EleonoreMizo/pedalevite/src/mfx/dsp/nz/README.md

## nz — noise generators

- **`GaussFast`**: fast gaussian noise approximation
- **`PinkShade`**: accurate pink noise generator
- **`WhiteFast`**: rough but very fast white noise generator
