EleonoreMizo/pedalevite/doc/v1/datasheets/DFRobot 128x64 display/12864B_Graphic_LCD_Module_Dimensions.jpg

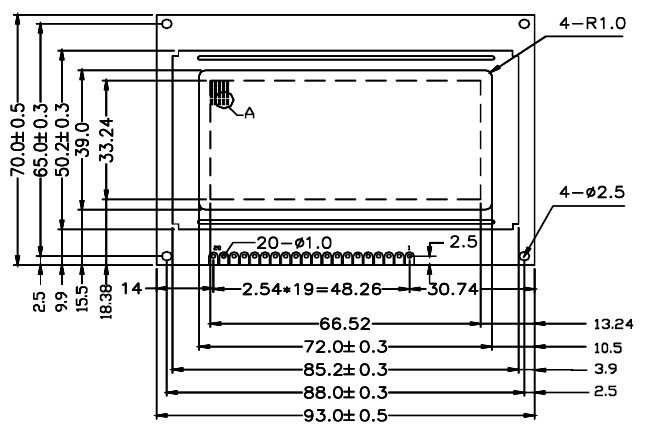
doc/v1/datasheets/DFRobot 128x64 display/12864B_Graphic_LCD_Module_Dimensions.jpg
