EleonoreMizo/pedalevite/doc/v1/datasheets/Toowei T601/ABUIABACGAAg-rylwQUoh9G9lAcwxgU46QE.jpg

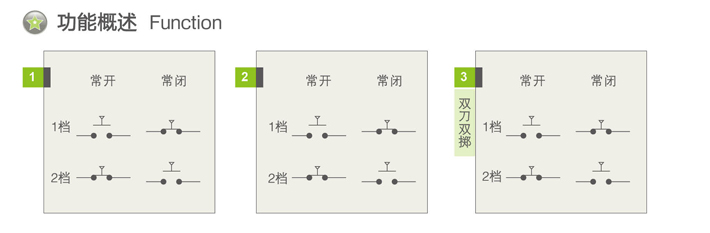
doc/v1/datasheets/Toowei T601/ABUIABACGAAg-rylwQUoh9G9lAcwxgU46QE.jpg
