EleonoreMizo/pedalevite/doc/v1/datasheets/Toowei T601/ABUIABACGAAg_rylwQUorPvk0wEwxgU44gU.jpg

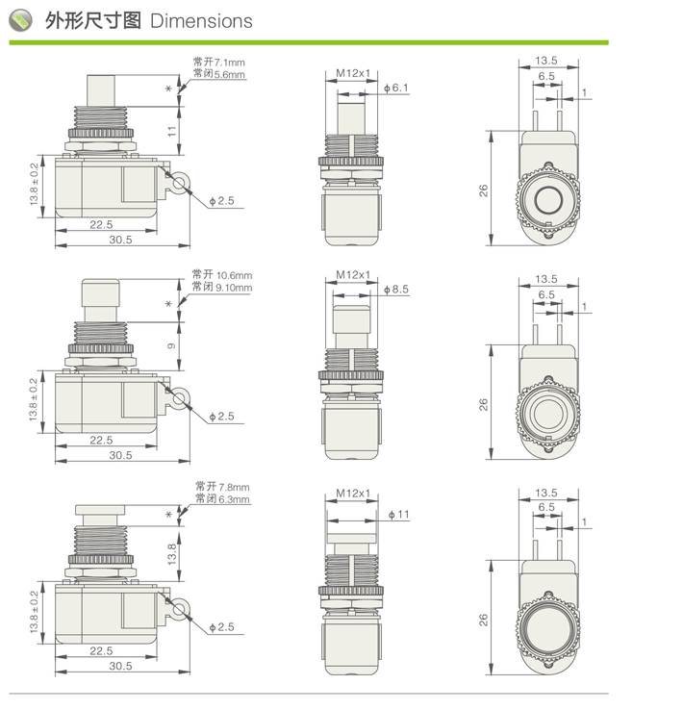
doc/v1/datasheets/Toowei T601/ABUIABACGAAg_rylwQUorPvk0wEwxgU44gU.jpg
