EleonoreMizo/pedalevite/doc/v1/datasheets/Toowei T601/ABUIABACGAAggbfIvgUoiN_t6AIw6AI4-AE.jpg

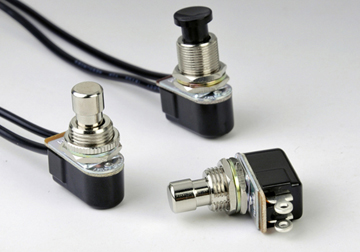
doc/v1/datasheets/Toowei T601/ABUIABACGAAggbfIvgUoiN_t6AIw6AI4-AE.jpg
