EleonoreMizo/pedalevite/doc/v1/datasheets/Toowei T601/ABUIABACGAAggL2lwQUo4-u1sgYwxgU4ywE.jpg

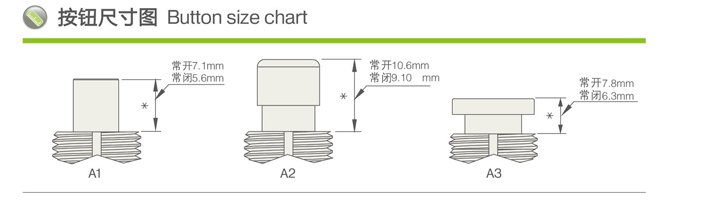
doc/v1/datasheets/Toowei T601/ABUIABACGAAggL2lwQUo4-u1sgYwxgU4ywE.jpg
