EleonoreMizo/pedalevite/doc/v1/datasheets/Toowei T601/ABUIABACGAAggr2lwQUolMDTvAcwxgU40AE.jpg

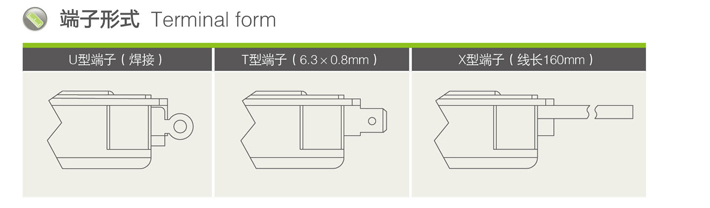
doc/v1/datasheets/Toowei T601/ABUIABACGAAggr2lwQUolMDTvAcwxgU40AE.jpg
