EleonoreMizo/pedalevite/doc/v1/datasheets/Toowei T601/ABUIABACGAAgt6LAwAUotr7NzQMwxgU4vwI.jpg

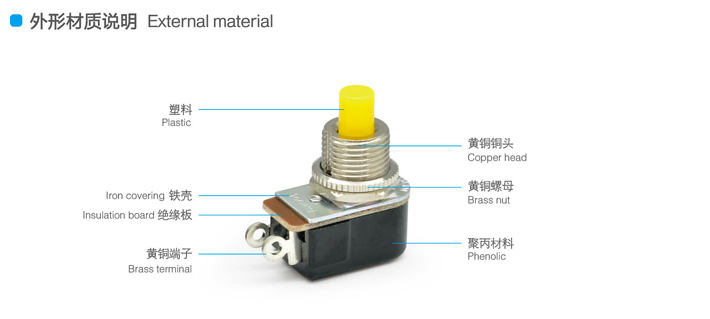
doc/v1/datasheets/Toowei T601/ABUIABACGAAgt6LAwAUotr7NzQMwxgU4vwI.jpg
