EleonoreMizo/pedalevite/doc/v1/datasheets/Toowei T601/ABUIABACGAAgtaLAwAUo_Jv2oAEwxgU4yAE.jpg

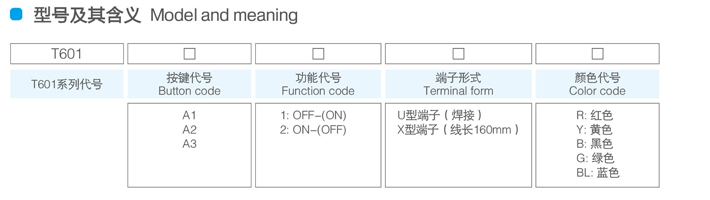
doc/v1/datasheets/Toowei T601/ABUIABACGAAgtaLAwAUo_Jv2oAEwxgU4yAE.jpg
