EleonoreMizo/pedalevite/doc/v1/datasheets/Toowei T601/ABUIABACGAAgtY63wAUo7P-HVTDGBTjEBw.jpg

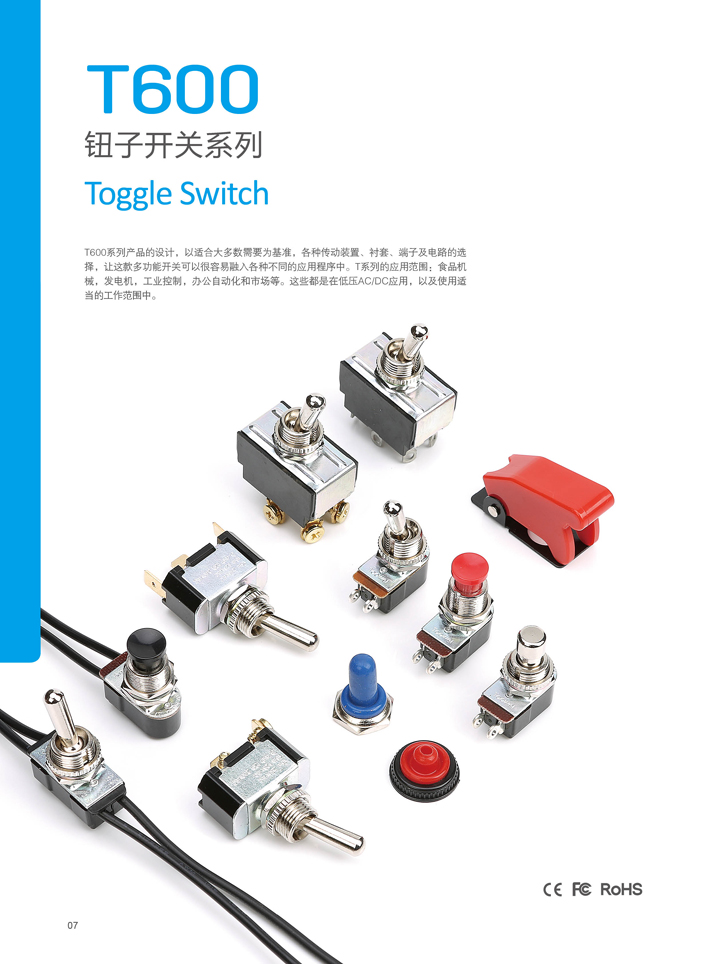
doc/v1/datasheets/Toowei T601/ABUIABACGAAgtY63wAUo7P-HVTDGBTjEBw.jpg
