EleonoreMizo/pedalevite/doc/v1/datasheets/Toowei T601/ABUIABACGAAguaLAwAUoiPfkyAMwxgU4rgI.jpg

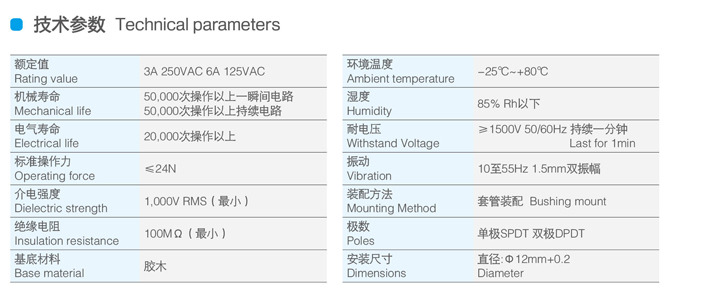
doc/v1/datasheets/Toowei T601/ABUIABACGAAguaLAwAUoiPfkyAMwxgU4rgI.jpg
