EleonoreMizo/pedalevite/doc/v1/building-instructions/index-eng.html

# Pédale Vite — Building instructions

## Table of content

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

## I. Introduction

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

## II. Required materials

The project’s GitHub repository (https://github.com/EleonoreMizo/pedalevite/) contains all the required files.

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

Some documents have been exported to .png or .pdf for convenience.

### Drawings

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

### Materials

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

### Tools

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

## III. Step-by-step building

### Enclosure

#### Machining

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

Pictures with some elements mounted:





#### Folding

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

The plate (without anything mounted) will be sandwiched between two devices.

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

#### Side stands

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

#### Stand for the Pi

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

### Electronics

#### Prototyping board cutting

Cut the prototyping boards in order to obtain the following pieces:

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



#### Soldering

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

#### Connection checks

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

#### LED board

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

#### Rotary encoder board

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

#### Display fix board

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

#### Wiring

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

### Assembly

#### First assembly

Most parts can now be screwed to the enclosure: boards, plugs, switches…



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

#### Soldering the switches

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

Also, depending on the model you got, the plastic box may be quite sensitive to heat and could melt easily. If one of the pin just slightly moves during soldering, the contact may be damaged. If it happens on DPDT switches, you can desolder it and try the other path. Always check the contact with a multimeter once both pins are soldered.

When all footswitch wires are soldered, they can be grouped by connector.



#### Soldering the power cables

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

Finally, connect the switch to the C14 socket using the remaining pins.

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



#### Soldering the audio cables

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

Solder a male jack plug to each of these cables.

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

Finally, solder the cables for the expression pedals.



#### Internal USB cable

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

Finally, solder the cable screen to the plug.

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



#### Power supply for the audio interface

Build a cable with three parts the following way:

First part is the power supply whose plug has been cut. Strip the wires.

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

Possibly: add an RC filter (not described here) if the power supply is too cheap.

#### Base of the enclosure

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

Calibrate the audio interface (gain and volume knobs) before closing the box.

For the enclosure feets, you can use specific rubber parts fitting on the screws.

## IV. Software setup

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

### Preparing the system

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

Unpack somewhere the .img file contained in the archive.

First format the card, if not previously done:

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

### Startup and base configuration

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

Log in with the default identifiers (pi / raspberry).

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

sudo nano /boot/config.txt

Modify the following lines by commenting or uncommenting them, as follows:

dtparam=i2c_arm=on
dtparam=spi=on
#dtparam=audio=on

Therefore the default audio device is removed. This is important because it simplifies our audio interface installation. Then, we ask to load the I2C module during boot:

sudo nano /etc/modules

Add the following lines at the end of the file:

i2c-bcm2708
i2c-dev

We now ask to boot to the command line to avoid loading the graphical interface subsystem:

sudo systemctl set-default multi-user.target
sudo ln -fs /lib/systemd/system/getty@.service \
/etc/systemd/system/getty.target.wants/getty@tty1.service

Now you can set your language and keyboard preferences (optional):

sudo raspi-config

Select 4. Localisation Options and set your language and keyboard preferences. Finally, hit the left arrow to select Finish. Reboot if the program requires it:

sudo shutdown -r now

### System update

Update the system:

sudo apt-get -y update
sudo apt-get -y dist-upgrade

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

### Installing the audio interface

Plug the interface. Open a console and type:

aplay -l

The USB interface should be on the list. Then, edit:

sudo nano /lib/modprobe.d/aliases.conf

Comment the line lowering the priority of USB interfaces:

#options snd-usb-audio index=-2

Reboot to validate the parameters.

sudo shutdown -r now

Log in again and type:

cat /proc/asound/modules

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

aplay -v -D plughw:0,0 file.wav

The sound should play fine, without any glitch.

### Software dependencies

Install git, Jack2, ALSA and autoconf :

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

wiringPi has its own installing procedure:

git clone git://git.drogon.net/wiringPi
cd wiringPi
./build

### Installing Pédale Vite

First, download the code in ~/Documents.

cd ~
mkdir Documents
cd Documents
git clone https://github.com/EleonoreMizo/pedalevite.git

Compile:

cd pedalevite/build/unix
./autogen.sh
./configure-release
make -j4

Note : the configure script was renamed configure-v1-release in later releases.

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

sudo /opt/pedalevite/bin/pedalevite

The program should run normally. Ctrl+C to stop it.

### Pédale Vite autostart

Create this file:

sudo nano /etc/init.d/pedalevite

Modify the file the following way:

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

case "$1" in
    start)
        echo "Mounting Pedale Vite directory as R/W..."
	mount --bind /opt/pedalevite/ /opt/pedalevite/
	mount -o remount,rw /opt/pedalevite/
	echo "Starting Pedale Vite..."
	/opt/pedalevite/bin/pedalevite &
	echo -n performance | sudo tee /sys/devices/system/cpu/cpu0/cpufreq/scaling_governor
	;;
    stop)
	echo "Stopping Pedale Vite"
	killall pedalevite
        umount /opt/pedalevite/
	;;
    *)
	echo "Usage: /etc/init.d/pedalevite start|stop"
	exit 1
	;;
esac

exit 0

Then:

sudo chmod +x /etc/init.d/pedalevite
sudo update-rc.d pedalevite defaults

Pédale Vite will run automatically at the next reboot. It can be run immediately, too:

sudo /etc/init.d/pedalevite start

### Boot time optimisation

Edit the file:

sudo nano /etc/modprobe.d/raspi-blacklist.conf

Add the following lines to deactivate WiFi and Bluetooth :

#wifi
blacklist brcmfmac
blacklist brcmutil
#bluetooth
blacklist btbcm
blacklist hci_uart

### NOOBS removal

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

sudo fdisk -l

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

Mount the NOOBS partition:

sudo mkdir /mnt/noobs
sudo mount /dev/mmcblk0p1 /mnt/noobs

Create or modify autoboot.txt :

nano /mnt/noobs/autoboot.txt

Add the following line, possibly replacing the 6 with the desired partition number:

boot_partition=6

Reboot to check that everything is fine.

### Read-only operating system and other optimisations

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

sudo apt-get -y remove --purge wolfram-engine triggerhappy pi-bluetooth
sudo apt-get -y remove --purge cron anacron logrotate dphys-swapfile

Remove the X-server and related:

sudo apt-get -y remove --purge xserver-common lightdm
sudo insserv -r x11-common

Remove the now useless dependencies:

sudo apt-get -y autoremove --purge

Install busybox syslog instead of rsyslog :

sudo apt-get -y install busybox-syslogd
sudo dpkg --purge rsyslog

Change the location of the DHCP leases:

sudo rm -rf /var/lib/dhcp/
sudo rm -rf /var/lib/dhcpcd5/
sudo ln -s /tmp /var/lib/dhcp
sudo ln -s /tmp /var/lib/dhcpcd5
sudo rm /etc/resolv.conf
sudo ln -s /tmp/dhcpcd.resolv.conf /etc/resolv.conf

Replace some var subfolders with symbolic links on the RAM-disk:

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

Create or edit the /tmp/random-seed file at reboot:

sudo nano /lib/systemd/system/systemd-random-seed.service

Add a ExecStartPre line in [Services] :

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

Other details:

sudo nano /etc/init.d/checkroot.sh

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

case "$1" in
  start|"")
        #do_start
        ;;
  restart|reload|force-reload)

sudo nano /etc/init.d/checkfs.sh

Same, comment the do_start at the end if the file exists.

sudo nano /etc/init.d/checkroot-bootclean.sh

Comment the rm and the clean_all in the case start if the file exists

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

It’s not important if several of the commands above fail (“no such file or directory”).

sudo nano /etc/systemd/system/dhcpcd5.service

The file may also be called dhcpcd5. Modify it to put the PIDFile in /var :

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

sudo nano /etc/fstab

Add ,ro after the defaults for the disk patitions:

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

sudo nano /boot/cmdline.txt

Add fastboot noswap ro at the very end of the line:

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

mmcblk0p1 can change as well, depending on NOOBS.

sudo nano /etc/rc.local

Add the chmod before the exit 0:

  printf "My IP address is %s\n" "$_IP"
fi

chmod g+w,o+w /tmp
exit 0

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

sudo nano /etc/bash.bash_logout

Add the following lines at the end:

mount -o remount,ro /
mount -o remount,ro /boot

Notifies the changes to systemd:

sudo systemctl daemon-reload

Reboot. Pédale Vite is now functional.

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

Failed to get D-Bus connection: No such file or directory

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

sudo mount -o remount,rw /

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

sudo mount -o remount,rw /boot

## V. Maintenance

### Tests and troubleshooting

To do…

### Source code

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

#### Compiling

Project files are located in the pedalevite/build folder.

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

win contains the projects for Visual Studio 2013. Source code is organized according to seveal categories:

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

These three projects are bundled into the pedalevite.sln solution.

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

#elif (MAIN_API == MAIN_API_ASIO)
	mfx::adrv::DAsio  snd_drv;
	chn_idx_in = 2;
#else

The emulation uses the following keys:

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

#### Architecture

##### Threads

The program uses 3 main threads:

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

##### MVC paradigm

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

#### File tree

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

## VI. Possible improvements and variations

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

#### External audio interface

There would be some advantages to put the audio interface out of the perdalboard:

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

For the cons:

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

#### Cheaper parts

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

#### Rotary encoder removal

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

Less connections, less costs and a full board less. This is about 25€ saved.

#### Single PCB

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

Schematics remain the same, socket connectors too, excepted two of them.

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

#### Pull-up resistors

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

#### Soldering bridges for the display

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

#### Reducing the number of connectors

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

## VII. Version history

r3, 2020-01-16

- Added the creation of a few subdirectories for software installation.

r2, 2019-11-07

- Updated the autostart script to set the /opt/pedalevite subdirectory in R/W mode.

r1, 2017-09-24

- Document translation in English.

r0, 2016-12-31

- Document creation (in French).
