EleonoreMizo/pedalevite/doc/user-manual/sources/note.txt

screenshots.xcf :

– Crop
– Export to OpenRaster (.ora) format
– Rename the .ora to .zip
– Extract
– Use a spreasheet to turn the .xml index into a rename batch
