EleonoreMizo/pedalevite/doc/v1/user-manual/index.html

# Pédale Vite — manuel d’utilisation

## Table des matières

1. Introduction
2. Utilisation
  1. Description du matériel
  2. Démarrage
  3. Calibration
  4. Premiers pas
3. Référence
  1. Concepts
  2. Diodes lumineuses
  3. Écrans principaux
  4. Édition d’un programme
  5. Banques de programmes
  6. Configuration du pédalier
  7. Volumes et niveaux
  8. Réglages divers
  9. Accordeur
  10. Redémarrage
4. Effets disponibles
  1. All-Pass Distortion — Distorsion
  2. Color Me — Filtre de coloration vocale
  3. CompEx — Compresseur/Expanseur
  4. Convert To Stereo
  5. Delay — Écho stéréo
  6. Distortion Tone Stage — Tonalité pour distorsion
  7. Double Distortion
  8. Envelope Follower — Suiveur d’enveloppe
  9. Filter Squeezer — Filtre résonnant à distorsion
  10. FlanCho — Chorus et flanger
  11. Freeverb — Réverbération
  12. Frequency Shifter — Translateur de fréquences
  13. Harmonic Tremolo — Trémolo bi-bande
  14. Hypercomb — Filtre en peigne polyphonique
  15. Input Impedance Fix — Adaptation d’impédance d’entrée
  16. Noise Bleach — Barrière anti-bruit
  17. Noise Chlorine — Barrière anti-bruit
  18. Onset detector – Détecteur de début et de fin de note
  19. Parametric Equalizer — Égaliseur paramétrique
  20. Phaser AP
  21. Phaser HT
  22. Pitch Detector — Détecteur de hauteur de note
  23. Pulse Width Modulation Distortion
  24. Pulse Width Modulation Distortion 2
  25. SiemensGirlz — Écho créatif
  26. Simple Distortion
  27. Speaker Emulator — Émulation de haut-parleur
  28. Test Generator — Générateur de tonalités de test
  29. Tremolo
  30. Wah-wah
  31. Wah-wah (CryBaby)
  32. ADSR — Enveloppe de contrôle
  33. Control ramp — Transition de paramètre
  34. LFO — Oscillateur basse fréquence
5. Dépannage
6. Historique des versions

## I. Introduction

Pédale Vite est une pédalier multi-effet pour guitare à fabriquer soi-même (DIY, do it yourself). Ce manuel détaille comment utiliser le pédalier une fois monté et fonctionnel.

## II. Utilisation

### Description du matériel

#### Face arrière

1. Ports USB et Ethernet du Rasberry Pi 3
2. Prises pour pédales d’expression
3. Interrupteur de mise en marche
4. Cordon d’alimentation secteur 220–240 V
5. Sorties audio vers ampli ou console
6. Sortie casque, stéréo en jack 6,35 mm.
7. Entrées guitare



L’accès au Pi n’est pas nécessaire en fonctionnement courant et ne sert qu’aux opérations de maintenance.

La première pédale d’expression se trouve à gauche sur le panneau, et donc à droite quand on fait face au pédalier.

Tous les jacks sont en 6,35 mm et sont asymétriques (signal mono), à part la prise casque qui est stéréo.

Les canaux gauches et droits des entrées et des sorties sont inversés afin qu’ils soient dans le bon ordre quand on se place devant le pédalier. Les entrées font environ 500 kΩ d’impédance. Utiliser le canal gauche pour brancher la guitare ou tout autre signal mono. Quand le pédalier est configuré en mono, les deux sorties diffusent le même signal.

#### Face supérieure

8. Bouton de contrôle des effets
9. Écran
10. Boutons rotatifs de navigation dans les menus
11. Boutons de navigation dans les menus
12. LED de contrôle, leur usage dépend du contexte.
13. Deux rangées de six pédales permettant de changer les effets.



Les boutons poussoir de navigation sont agencés de la façon suivante. Sur la rangée supérieure : Sélectionner/valider (Select), flèche haut (↑), annuler/échappement (Esc). Sur la rangée inférieure : flèches gauche (←), bas (↓), droite (→).

Les boutons rotatifs de navigation sont généralement redondants des boutons poussoir. Celui de gauche permet de se déplacer verticalement, et celui de droite horizontalement.

### Démarrage



1. Brancher le cordon d’alimentation (4) sur le secteur.
2. Brancher la guitare à l’entrée gauche (7).
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
