EleonoreMizo/pedalevite/doc/building-instructions/board-5v-wires.jpg

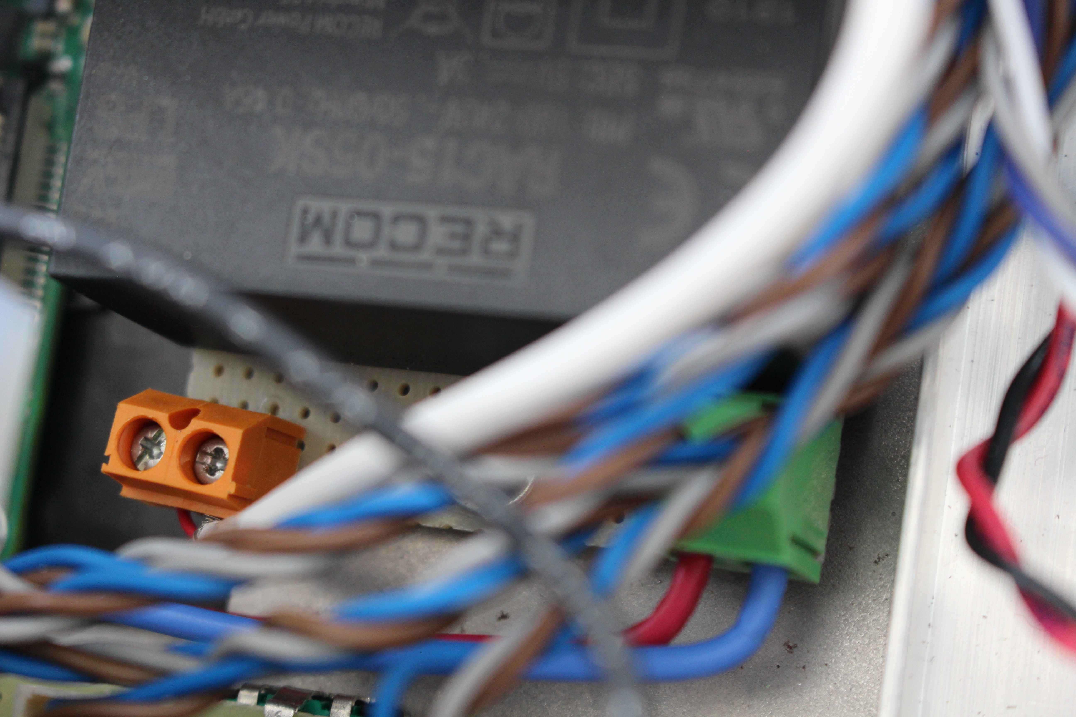
doc/building-instructions/board-5v-wires.jpg
