EleonoreMizo/pedalevite/doc/building-instructions/board-audio-input.jpg

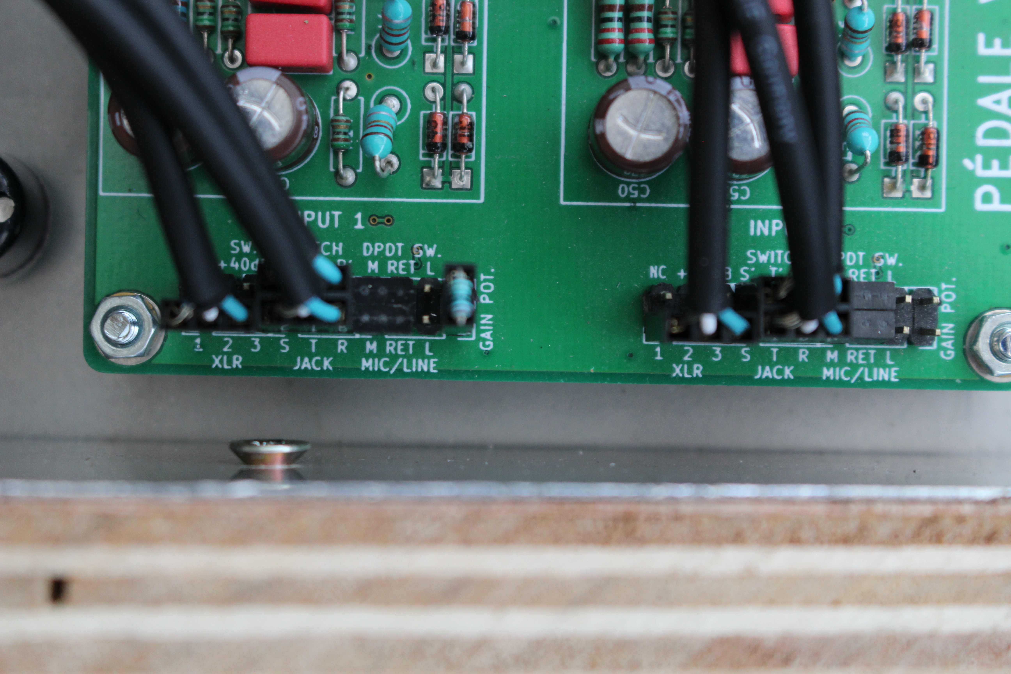
doc/building-instructions/board-audio-input.jpg
