EleonoreMizo/pedalevite/doc/building-instructions/board-audio-jumper-gnd.jpg

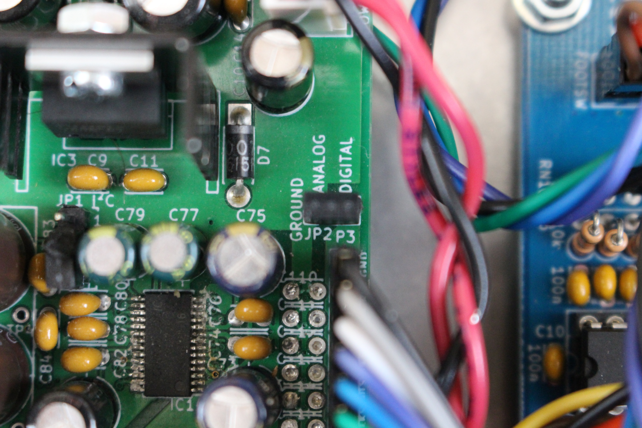
doc/building-instructions/board-audio-jumper-gnd.jpg
