EleonoreMizo/pedalevite/doc/building-instructions/board-audio-jumper-i2c.jpg

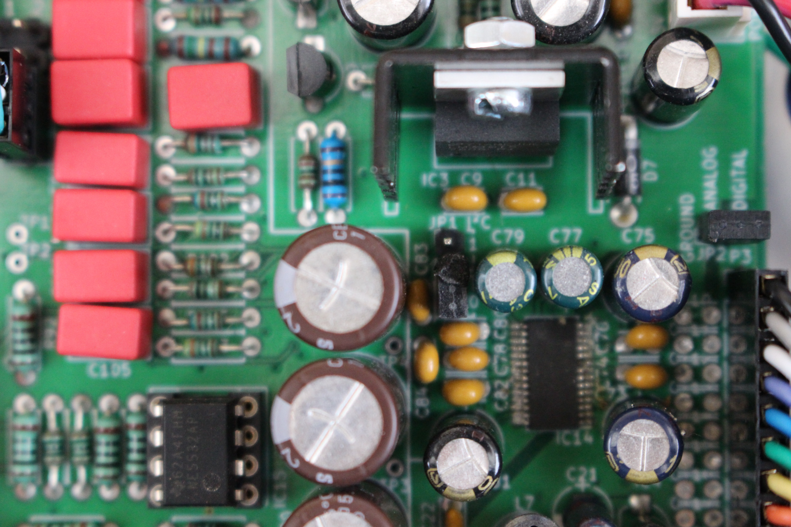
doc/building-instructions/board-audio-jumper-i2c.jpg
