EleonoreMizo/pedalevite/doc/building-instructions/board-audio-output.jpg

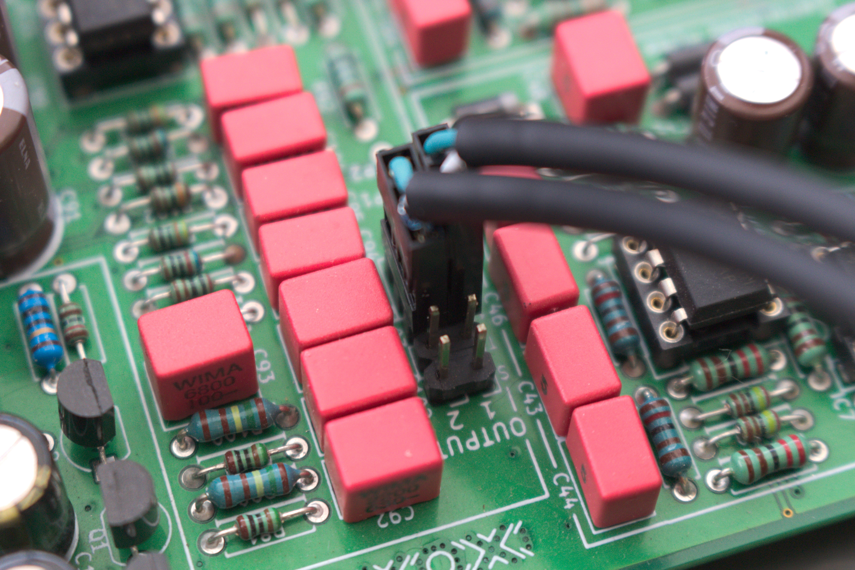
doc/building-instructions/board-audio-output.jpg
