EleonoreMizo/pedalevite/doc/building-instructions/board-audio.jpg

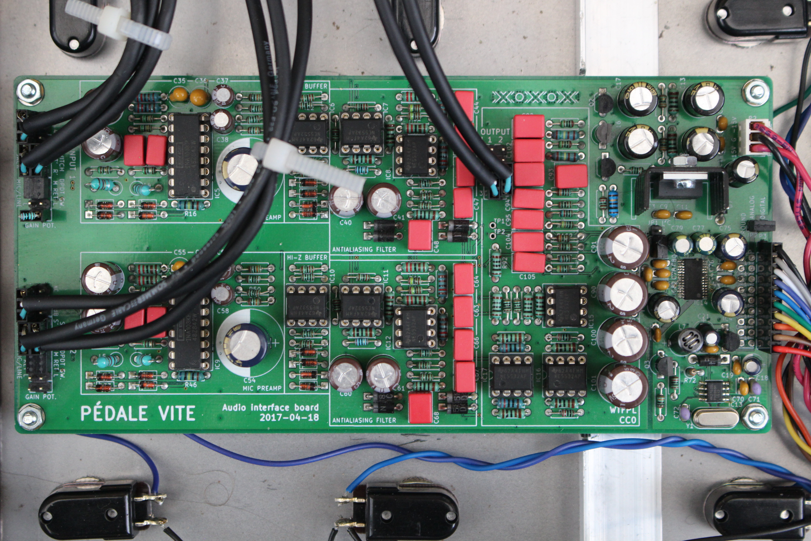
doc/building-instructions/board-audio.jpg
