EleonoreMizo/pedalevite/doc/building-instructions/board-rot-enc-nav.jpg

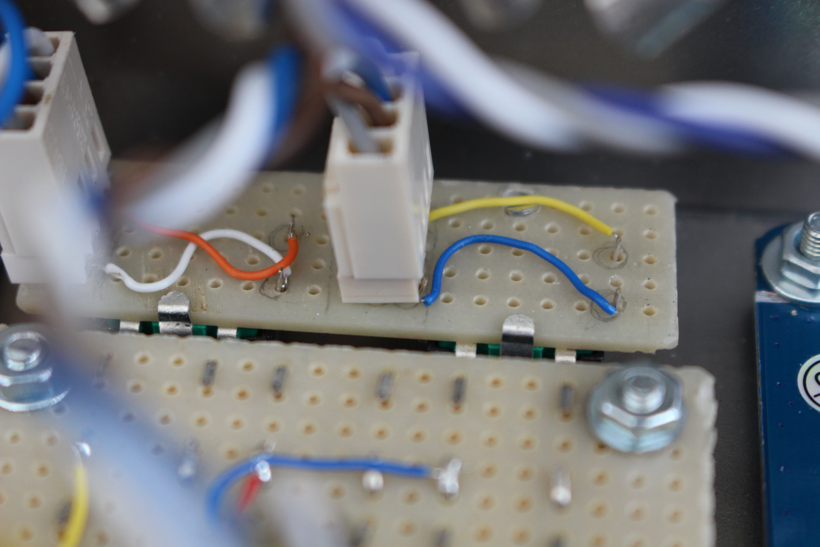
doc/building-instructions/board-rot-enc-nav.jpg
