EleonoreMizo/pedalevite/doc/building-instructions/board-rot-enc-param.jpg

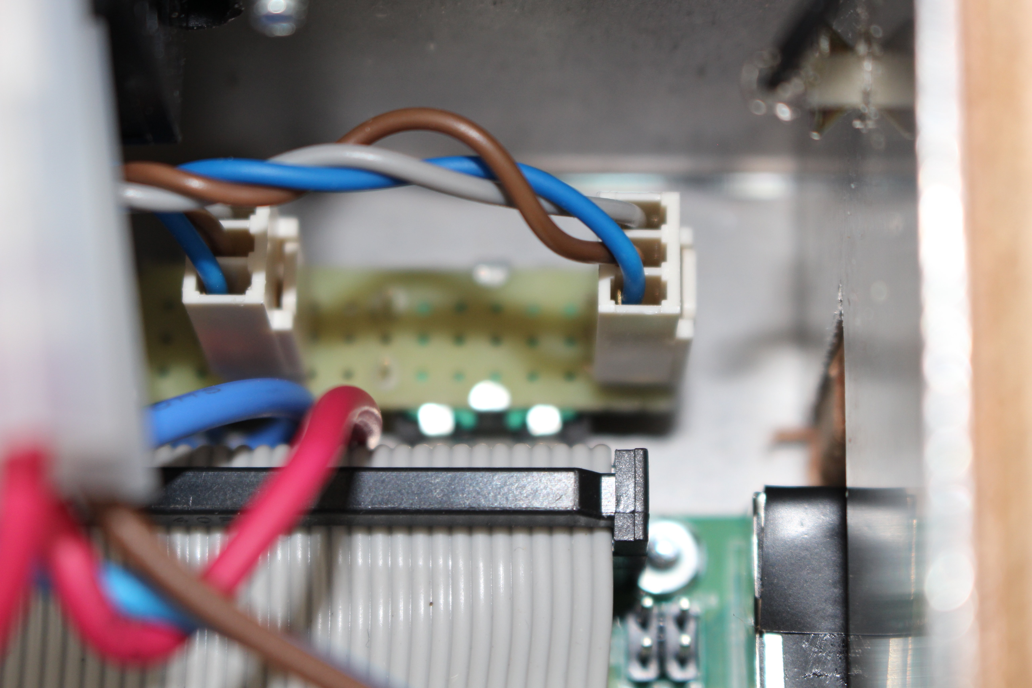
doc/building-instructions/board-rot-enc-param.jpg
