EleonoreMizo/pedalevite/doc/building-instructions/cables-mains.jpg

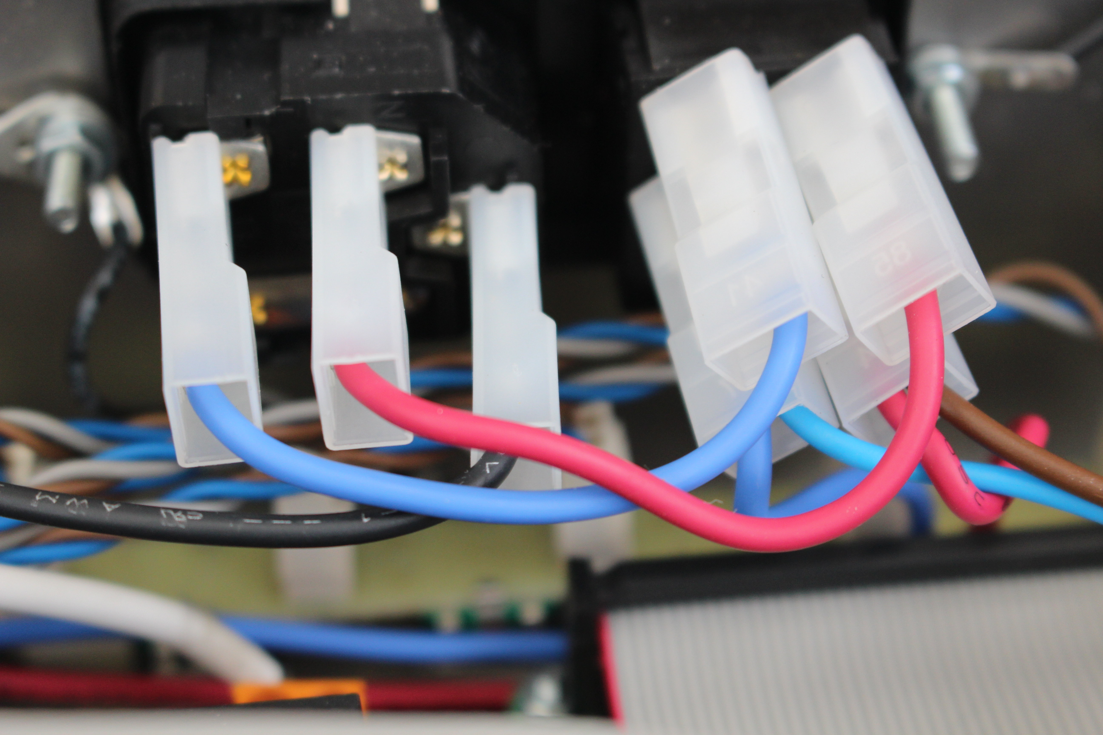
doc/building-instructions/cables-mains.jpg
