EleonoreMizo/pedalevite/doc/building-instructions/connectors-expression-pedals.jpg

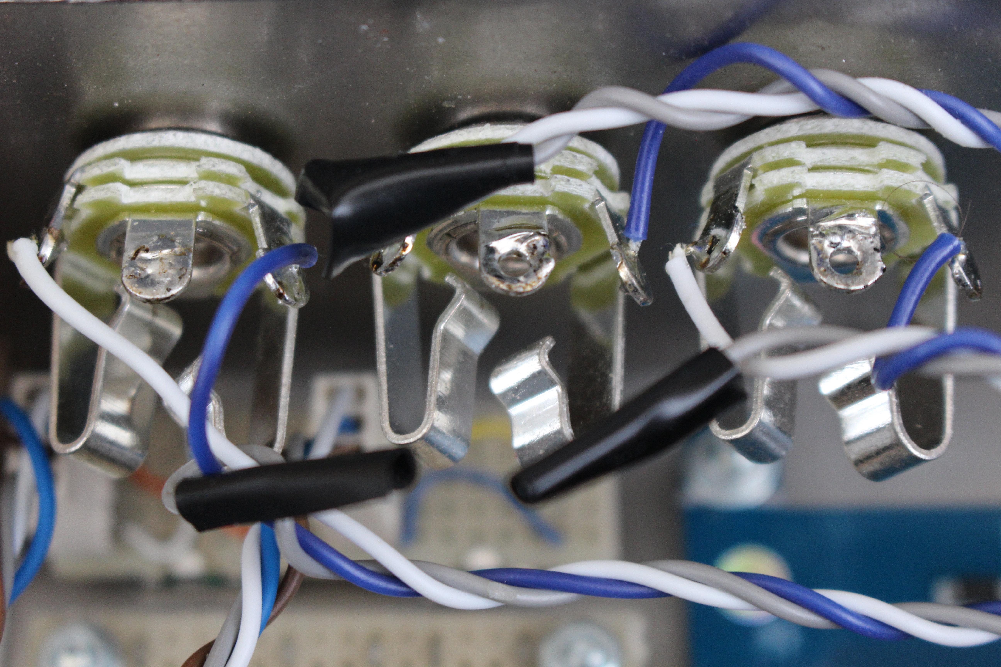
doc/building-instructions/connectors-expression-pedals.jpg
