EleonoreMizo/pedalevite/doc/building-instructions/connectors-missing-gain-pad.jpg

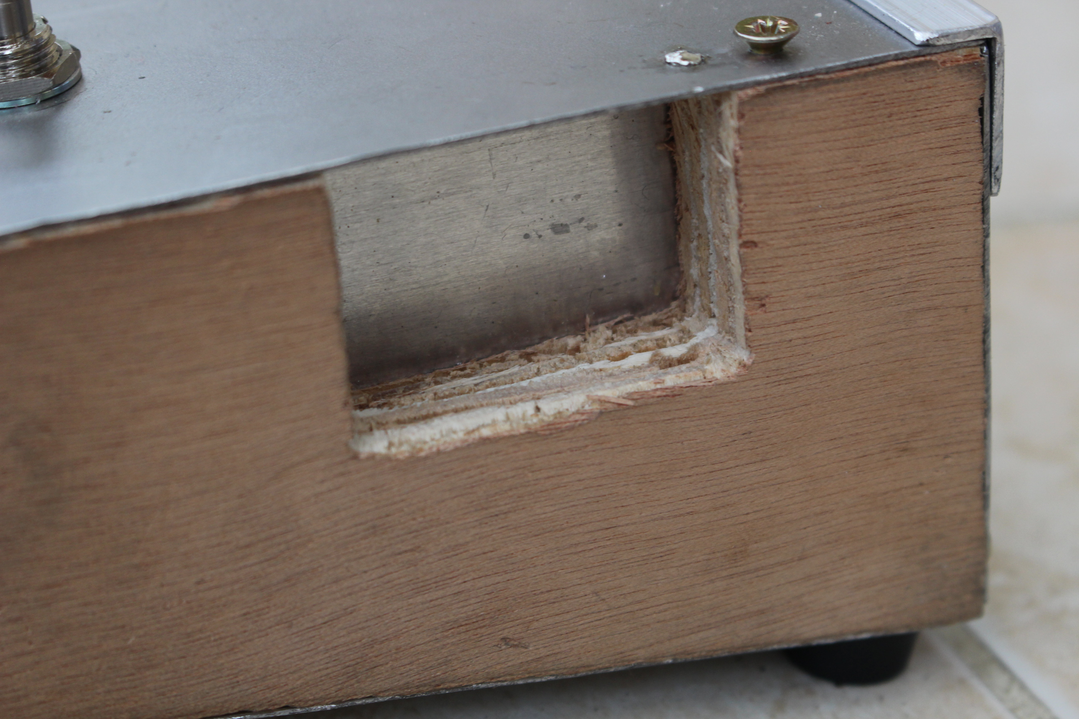
doc/building-instructions/connectors-missing-gain-pad.jpg
