EleonoreMizo/pedalevite/doc/building-instructions/connectors-rpi4.jpg

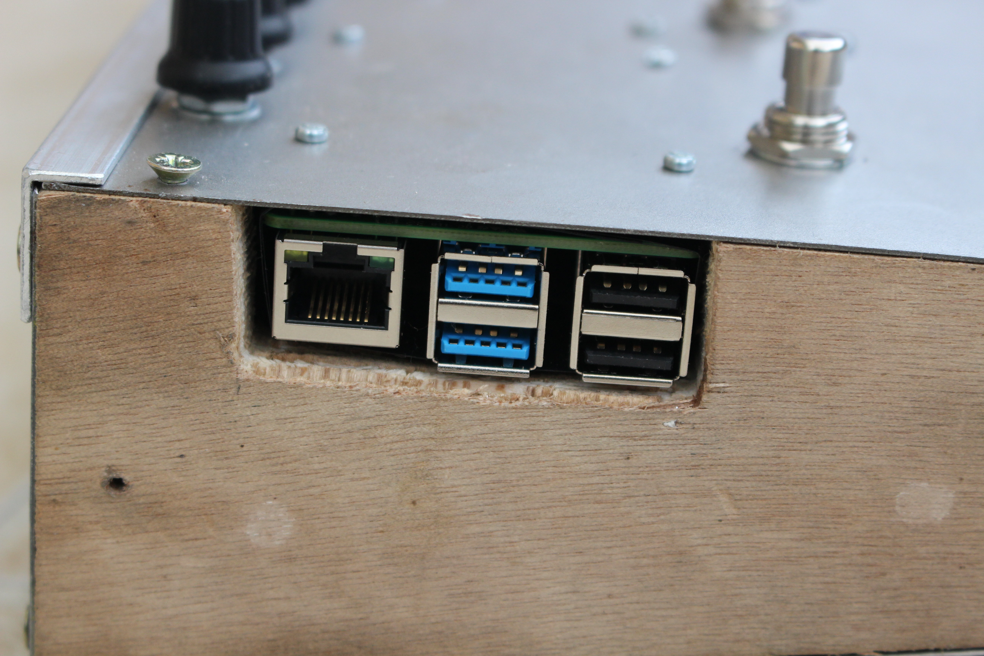
doc/building-instructions/connectors-rpi4.jpg
