EleonoreMizo/pedalevite/doc/building-instructions/display-ground-1.jpg

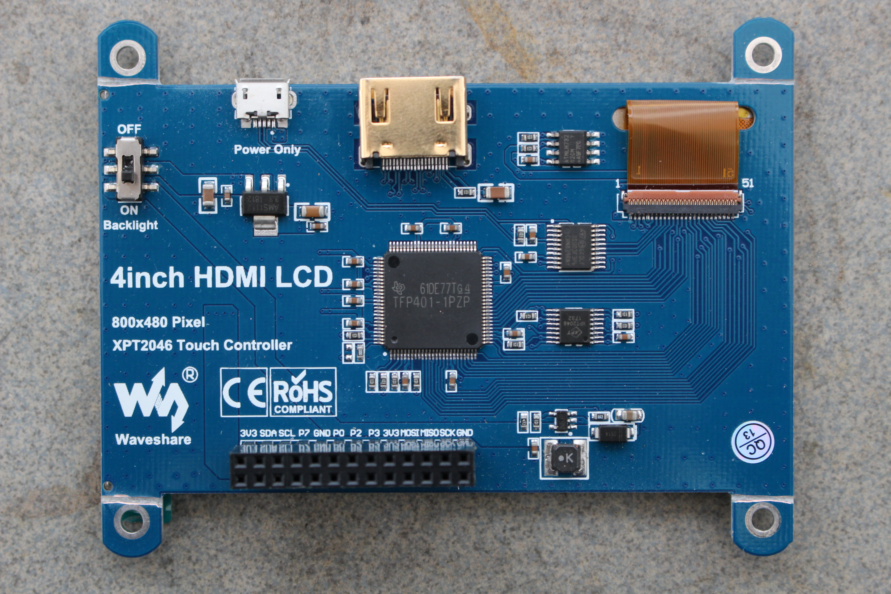
doc/building-instructions/display-ground-1.jpg
