EleonoreMizo/pedalevite/doc/building-instructions/display-ground-2.jpg

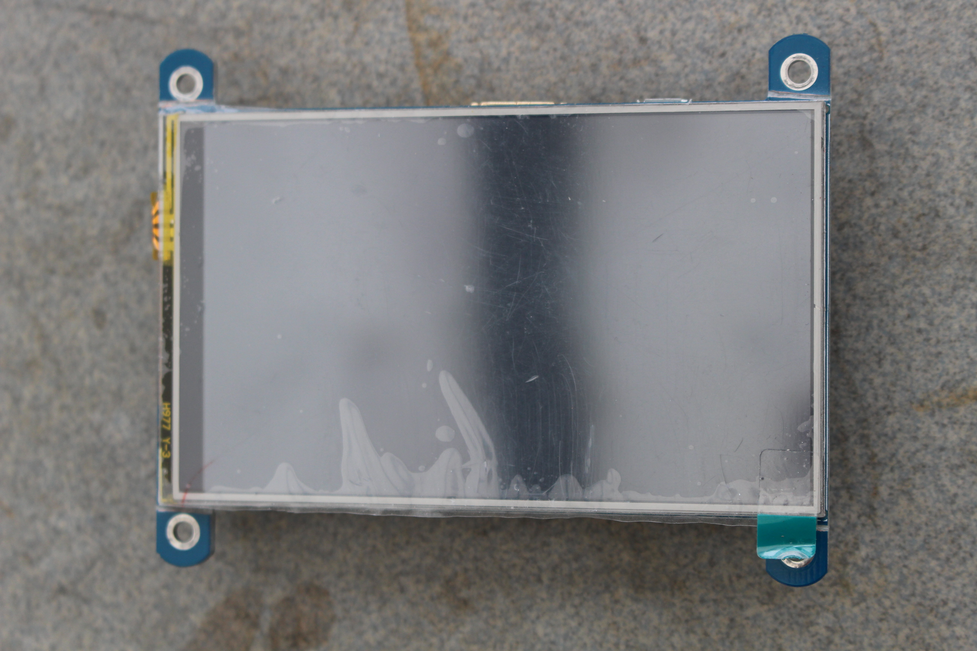
doc/building-instructions/display-ground-2.jpg
