EleonoreMizo/pedalevite/doc/building-instructions/display-outside.jpg

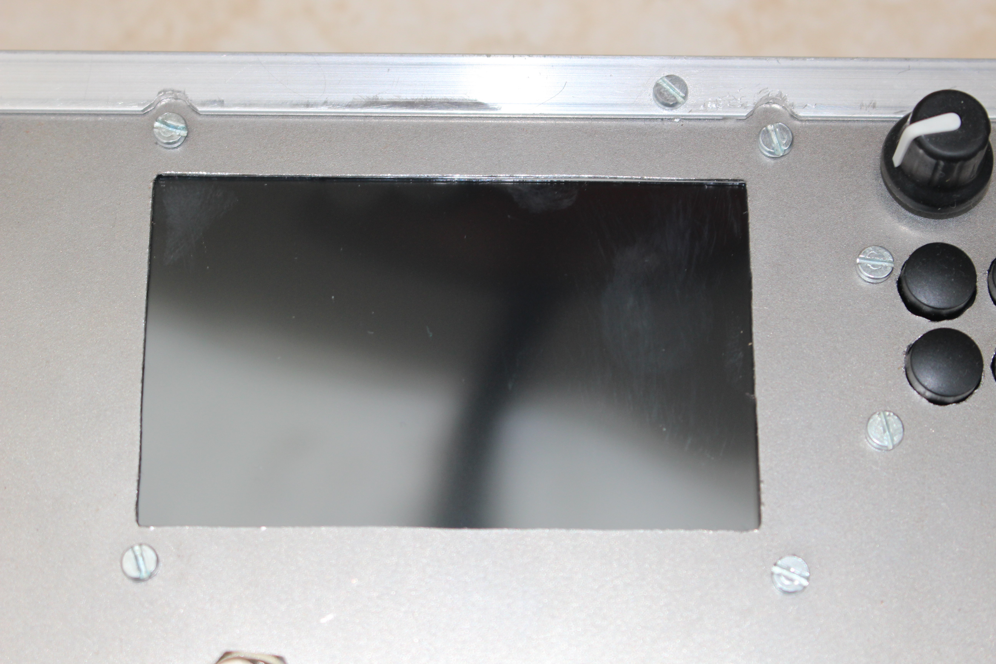
doc/building-instructions/display-outside.jpg
