EleonoreMizo/pedalevite/doc/building-instructions/enclosure-back.jpg

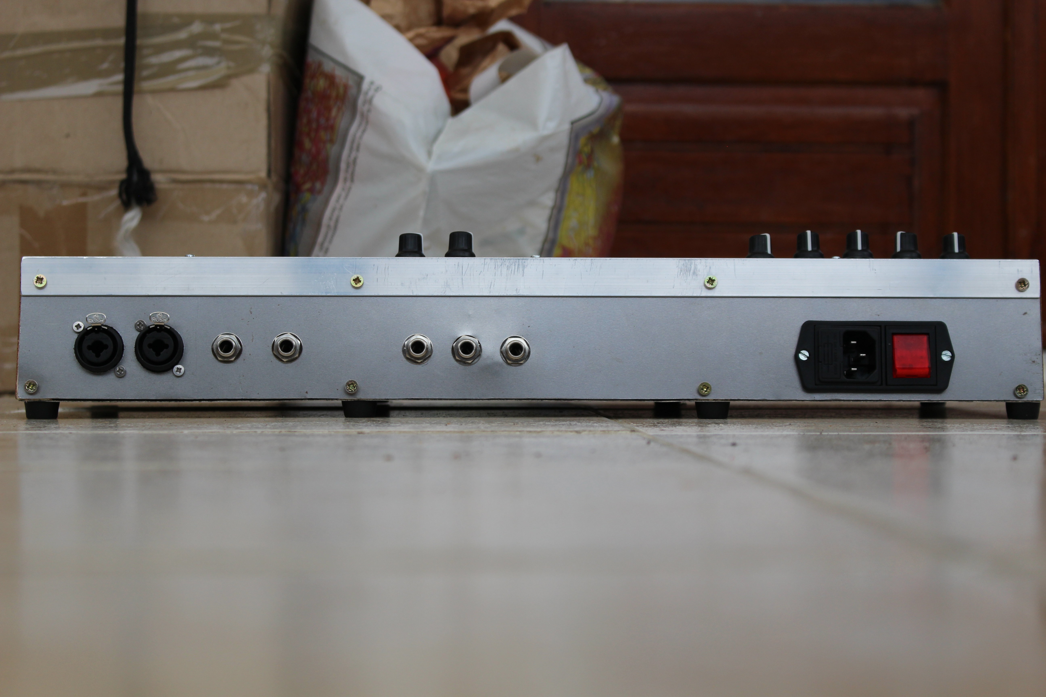
doc/building-instructions/enclosure-back.jpg
