EleonoreMizo/pedalevite/doc/building-instructions/enclosure-inside-boards-only.jpg

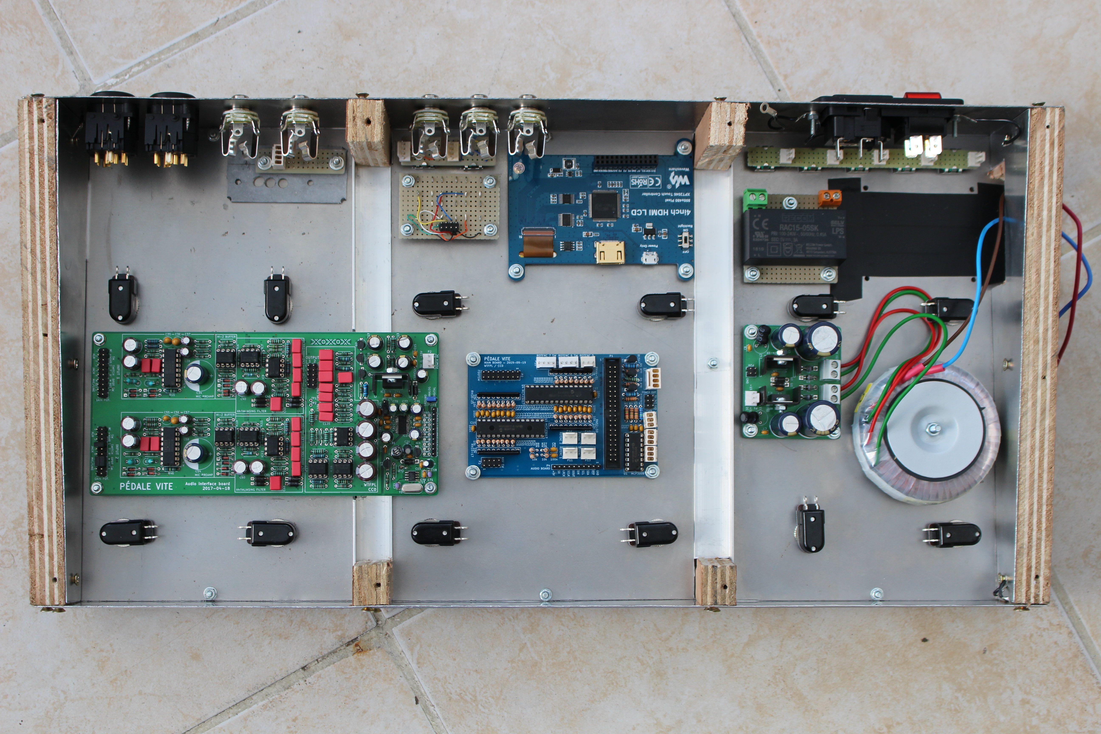
doc/building-instructions/enclosure-inside-boards-only.jpg
