EleonoreMizo/pedalevite/doc/building-instructions/enclosure-shielding-2.jpg

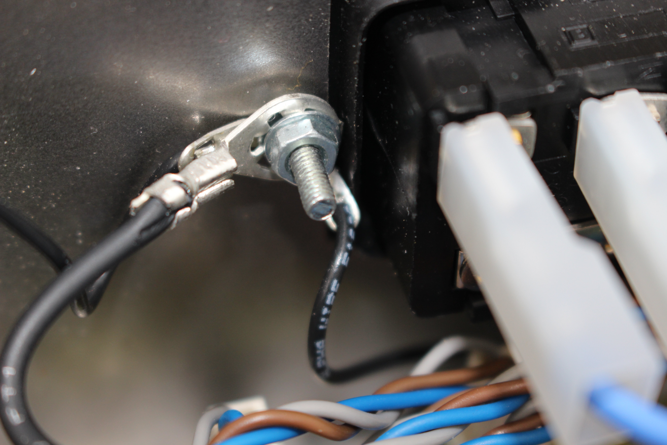
doc/building-instructions/enclosure-shielding-2.jpg
