EleonoreMizo/pedalevite/doc/building-instructions/enclosure-shielding-3.jpg

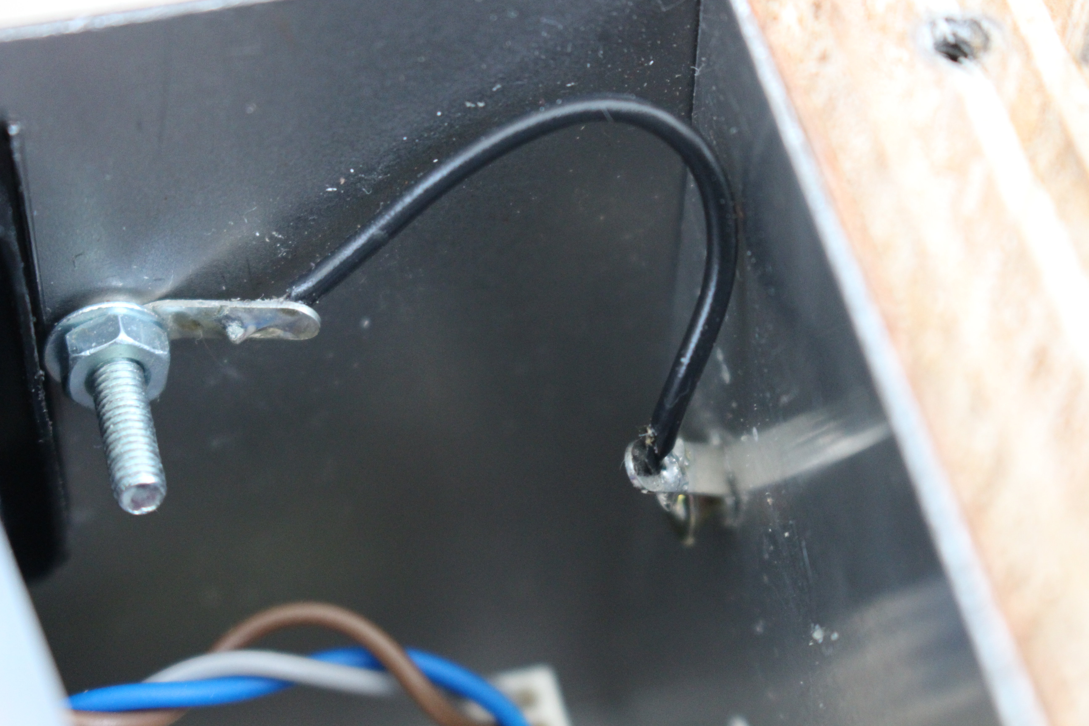
doc/building-instructions/enclosure-shielding-3.jpg
