EleonoreMizo/pedalevite/doc/building-instructions/enclosure-shielding-4.jpg

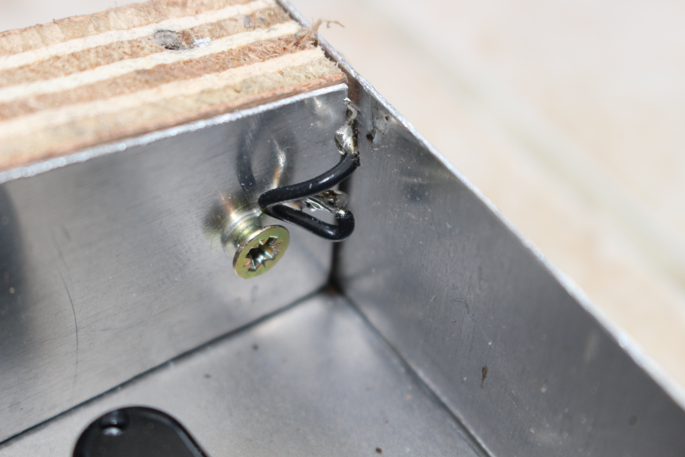
doc/building-instructions/enclosure-shielding-4.jpg
