EleonoreMizo/pedalevite/doc/building-instructions/enclosure-shielding-5.jpg

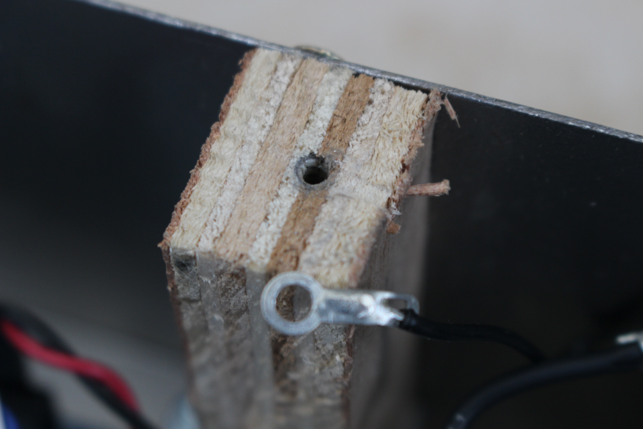
doc/building-instructions/enclosure-shielding-5.jpg
