EleonoreMizo/pedalevite/doc/building-instructions/enclosure-shielding-6.jpg

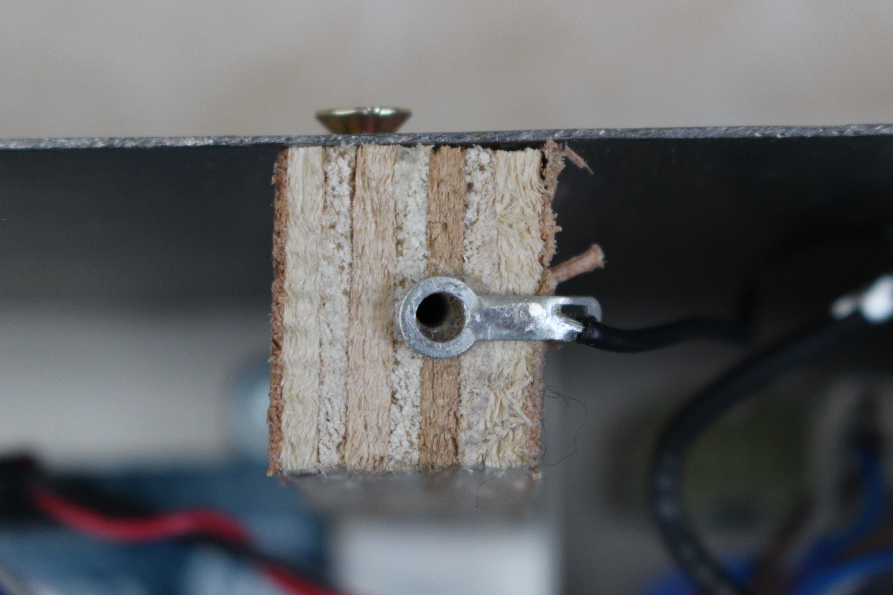
doc/building-instructions/enclosure-shielding-6.jpg
