EleonoreMizo/pedalevite/doc/building-instructions/footswitch-wiring.jpg

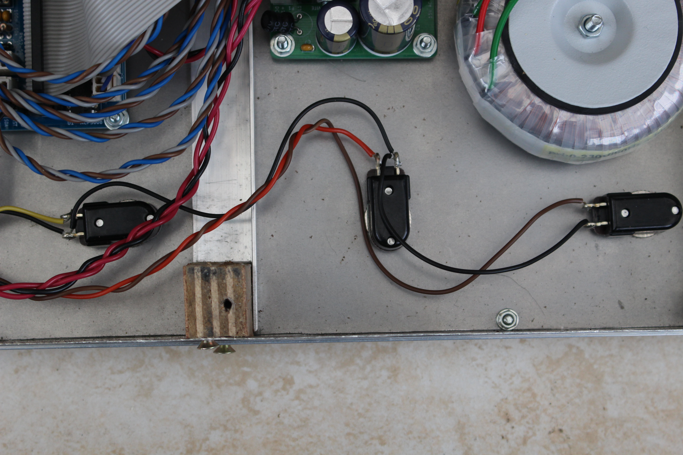
doc/building-instructions/footswitch-wiring.jpg
