EleonoreMizo/pedalevite/doc/building-instructions/ground-path.png

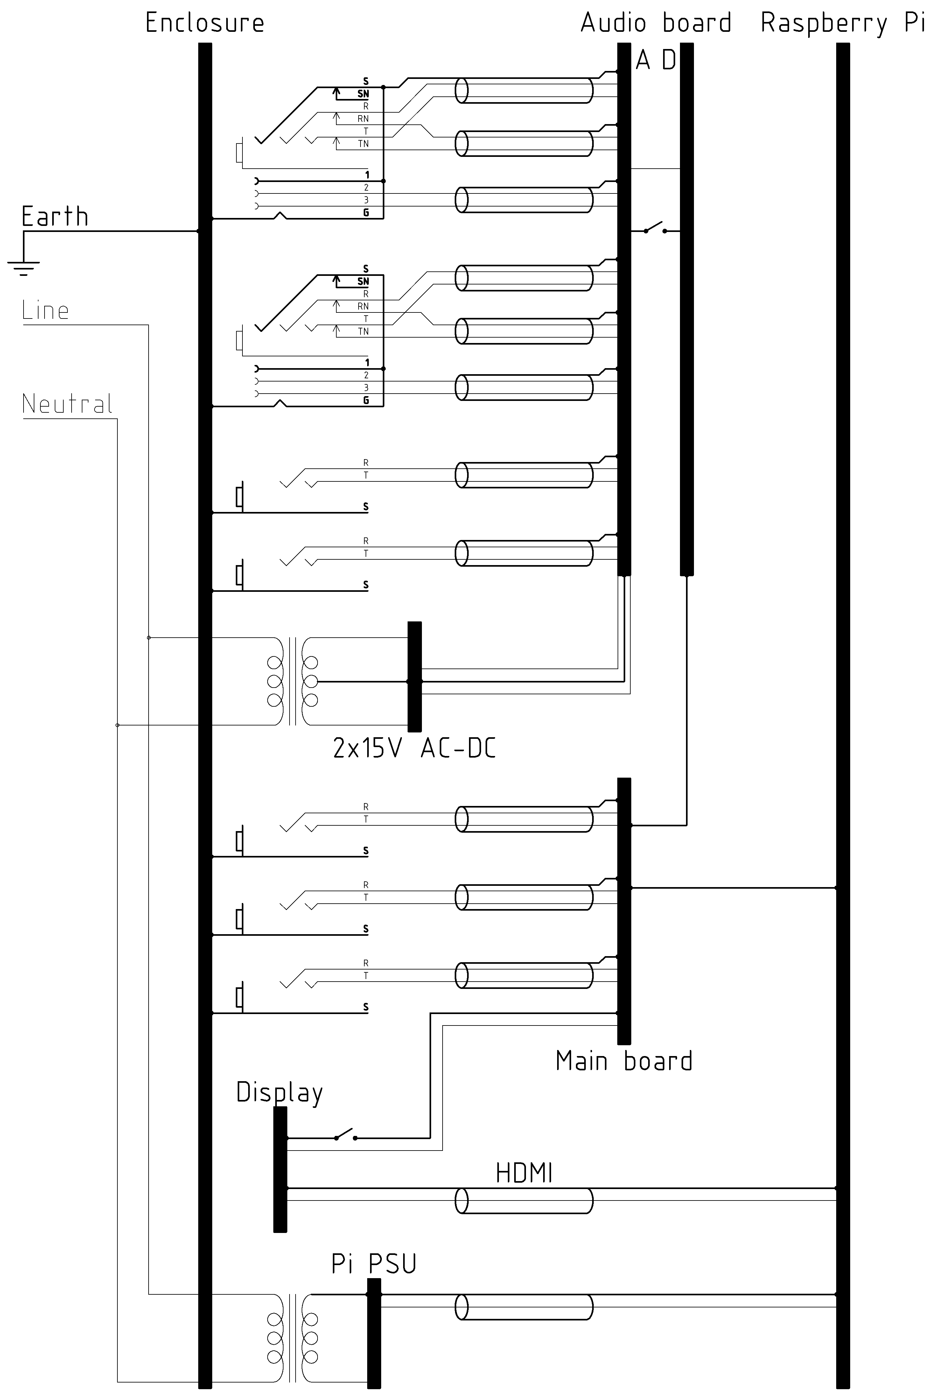
doc/building-instructions/ground-path.png
