EleonoreMizo/pedalevite/doc/building-instructions/led-board-mounted.jpg

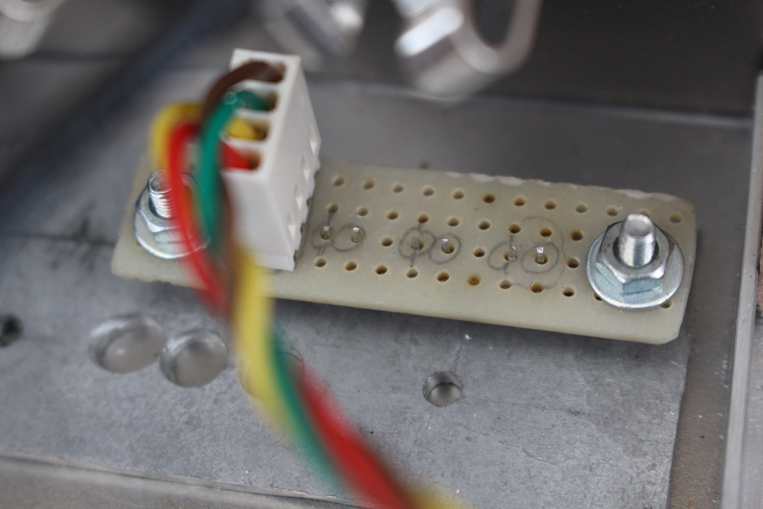
doc/building-instructions/led-board-mounted.jpg
