EleonoreMizo/pedalevite/doc/building-instructions/led-board.jpg

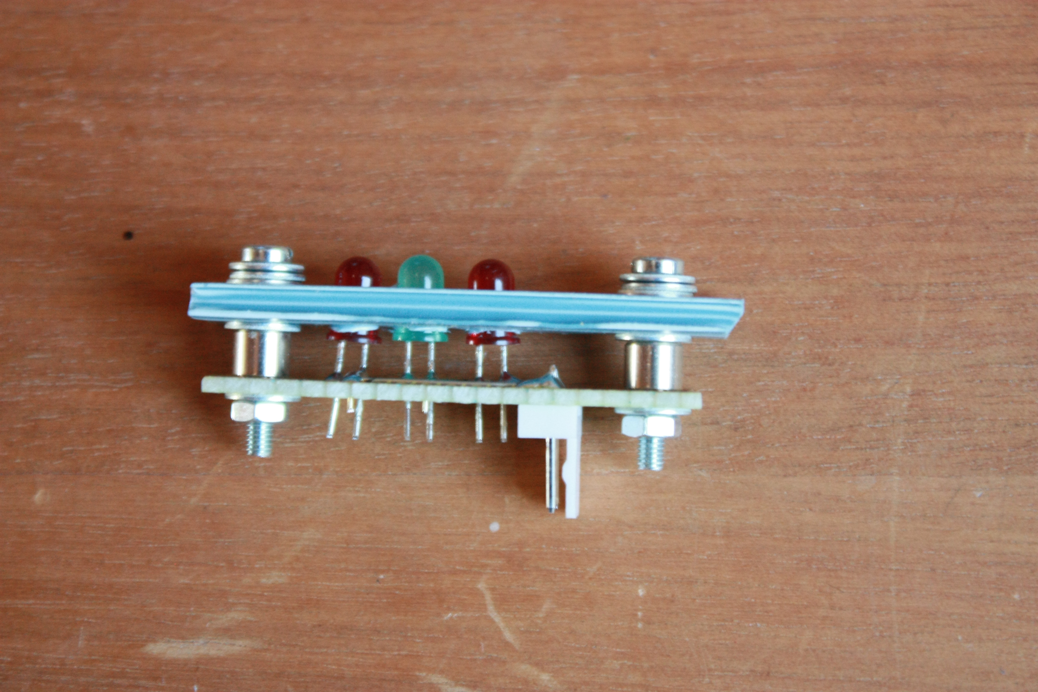
doc/building-instructions/led-board.jpg
