EleonoreMizo/pedalevite/doc/building-instructions/pedalevite-open.jpg

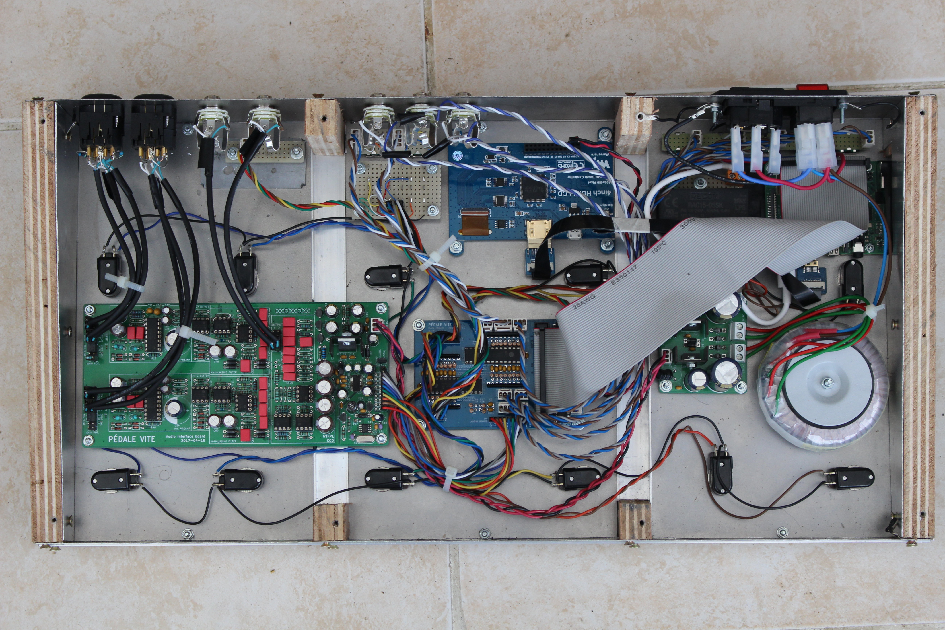
doc/building-instructions/pedalevite-open.jpg
