EleonoreMizo/pedalevite/doc/building-instructions/resistor-jumper.jpg

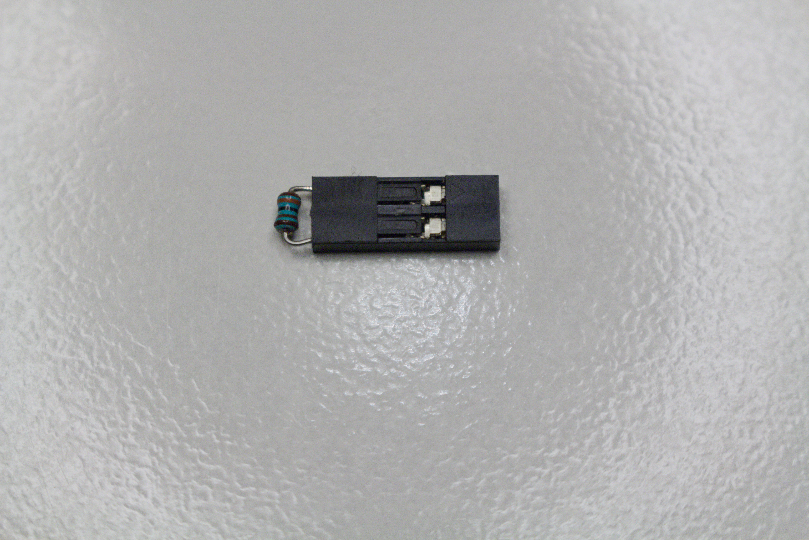
doc/building-instructions/resistor-jumper.jpg
