EleonoreMizo/pedalevite/doc/building-instructions/transformer-washer.jpg

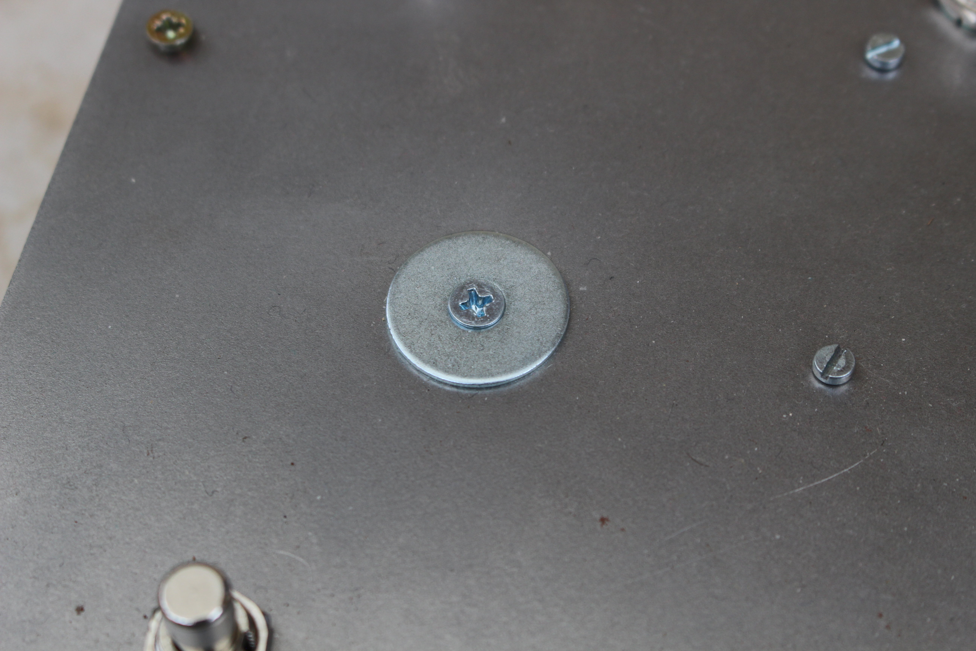
doc/building-instructions/transformer-washer.jpg
