EleonoreMizo/pedalevite/doc/building-instructions/unaligned-screws.jpg

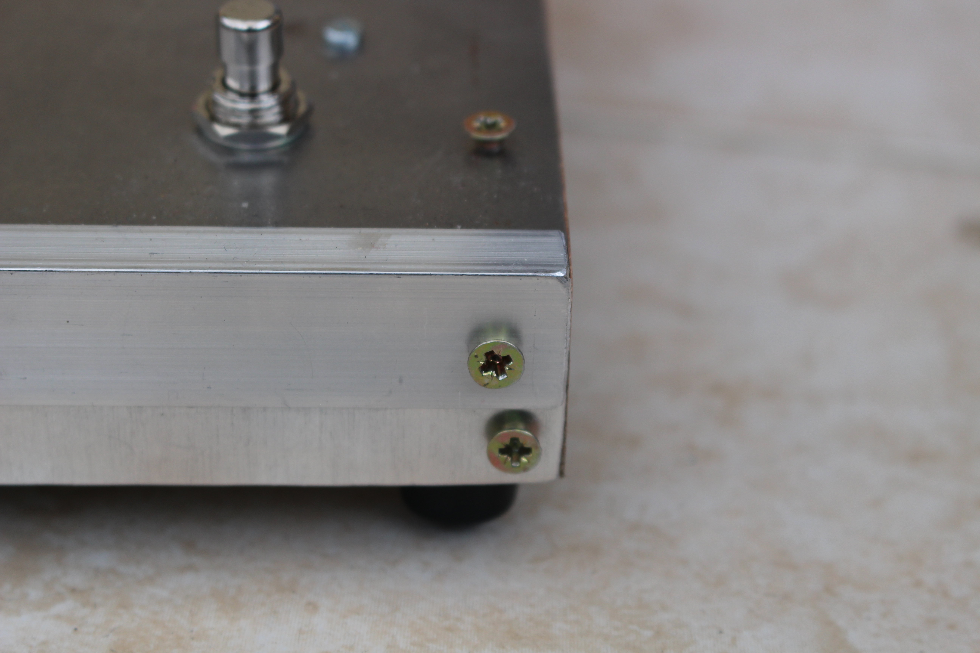
doc/building-instructions/unaligned-screws.jpg
