EleonoreMizo/pedalevite/doc/user-manual/panel-rear.png

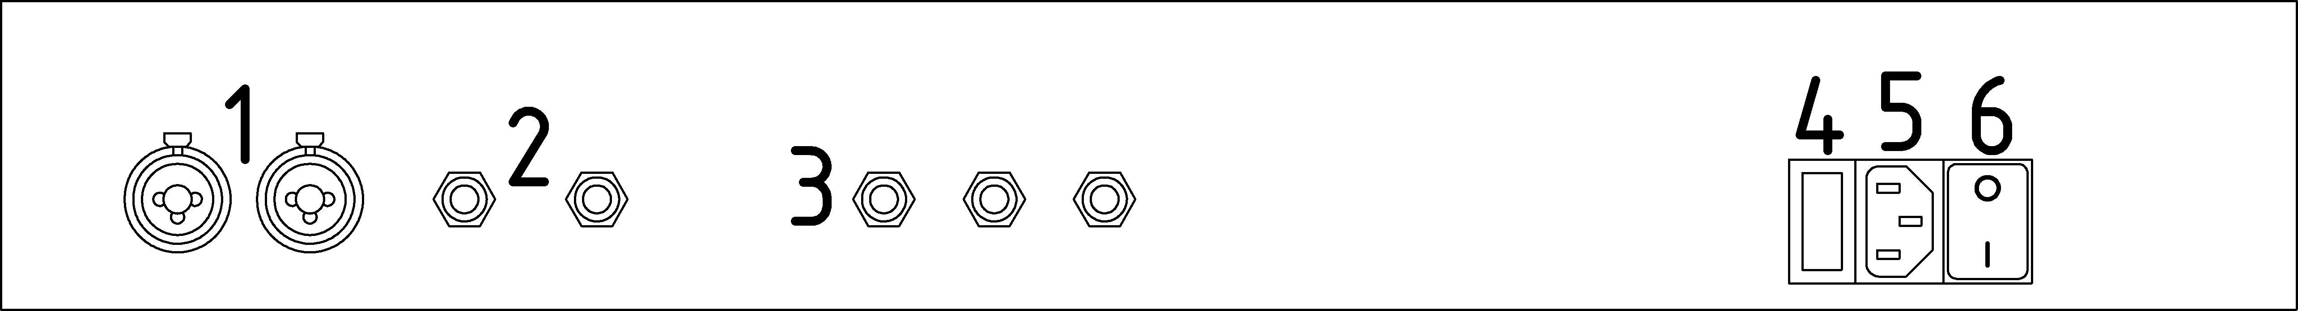
doc/user-manual/panel-rear.png
