EleonoreMizo/pedalevite/doc/user-manual/sources/panel.png

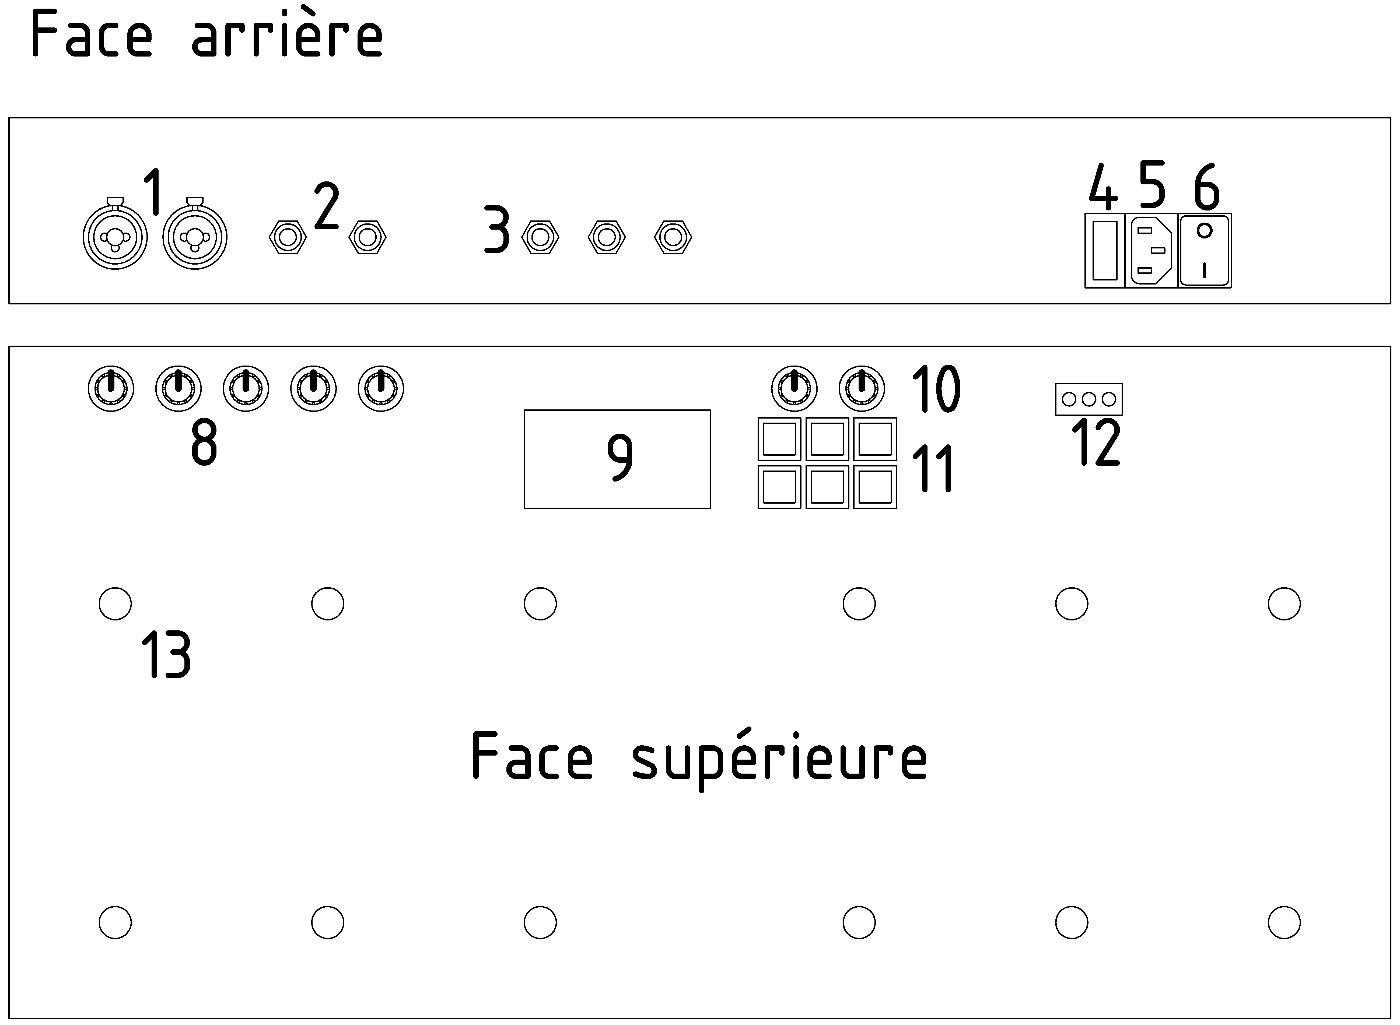
doc/user-manual/sources/panel.png
