EleonoreMizo/pedalevite/doc/user-manual/tuner-note.png

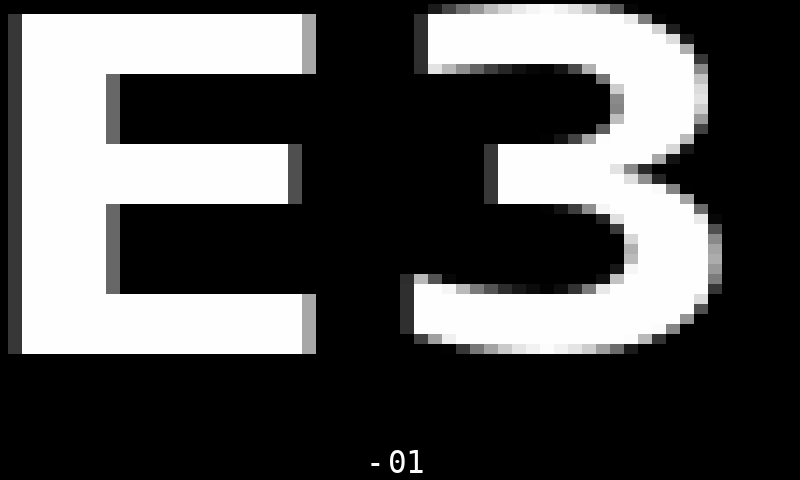
doc/user-manual/tuner-note.png
