EleonoreMizo/pedalevite/doc/v1/building-instructions/box-empty-inside.jpg

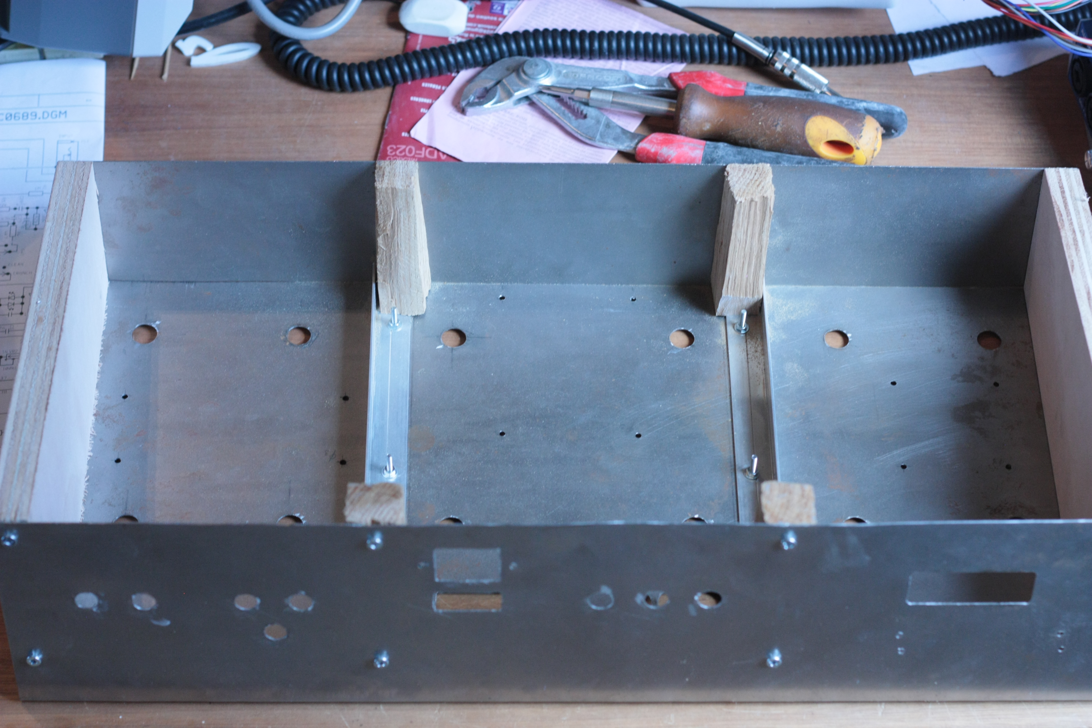
doc/v1/building-instructions/box-empty-inside.jpg
