EleonoreMizo/pedalevite/doc/v1/building-instructions/box-empty-top.jpg

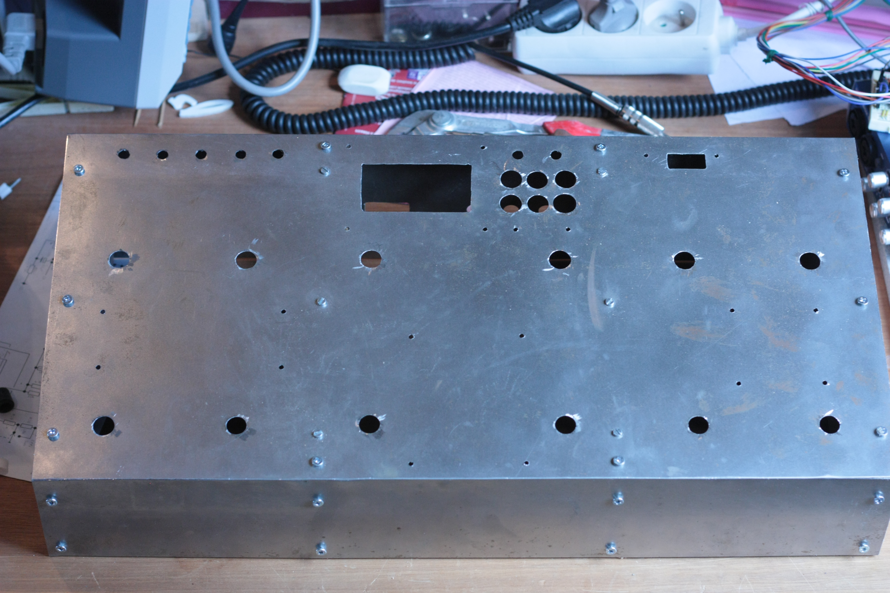
doc/v1/building-instructions/box-empty-top.jpg
