EleonoreMizo/pedalevite/doc/v1/building-instructions/box-inside-power-cables.jpg

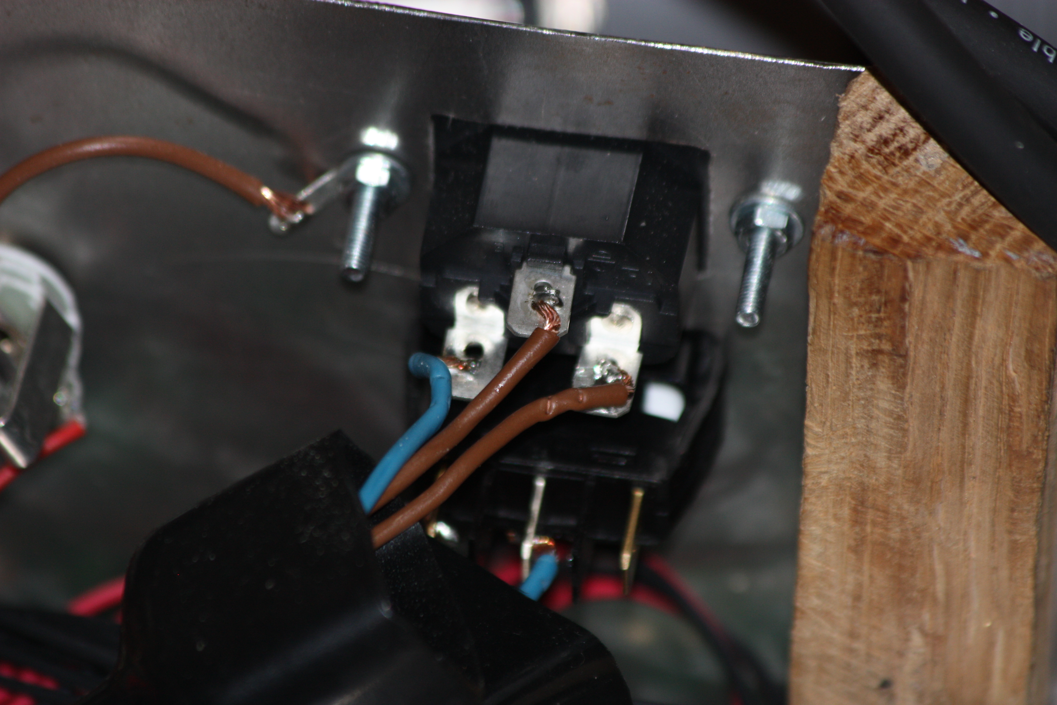
doc/v1/building-instructions/box-inside-power-cables.jpg
