EleonoreMizo/pedalevite/doc/v1/building-instructions/box-rear.jpg

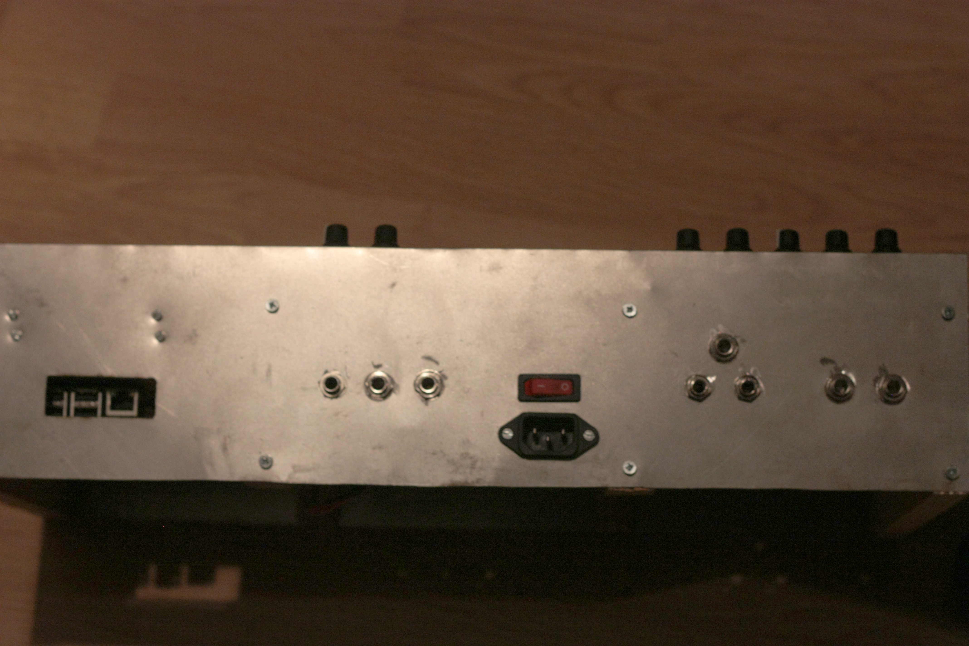
doc/v1/building-instructions/box-rear.jpg
