EleonoreMizo/pedalevite/doc/v1/building-instructions/panel-flat-inside.jpg

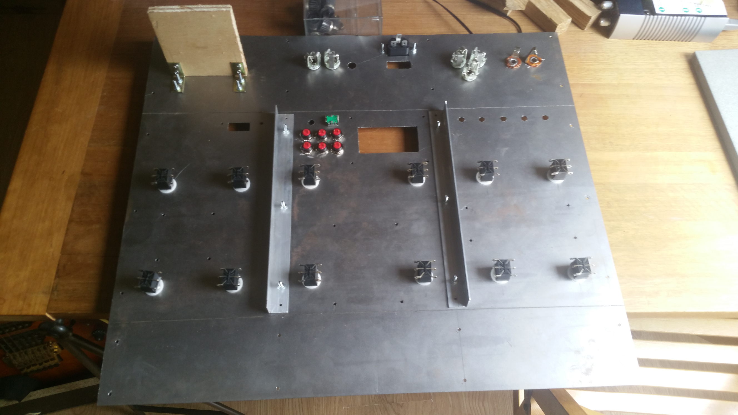
doc/v1/building-instructions/panel-flat-inside.jpg
