EleonoreMizo/pedalevite/doc/v1/building-instructions/panel-flat-outside.jpg

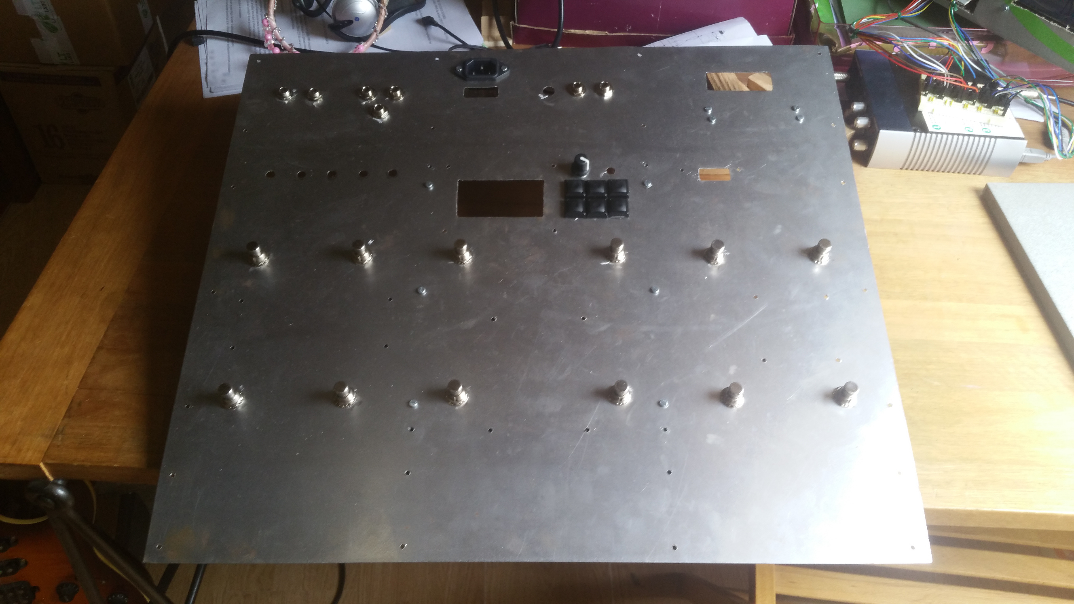
doc/v1/building-instructions/panel-flat-outside.jpg
