EleonoreMizo/pedalevite/doc/v1/building-instructions/usb-cable-plugged2.jpg

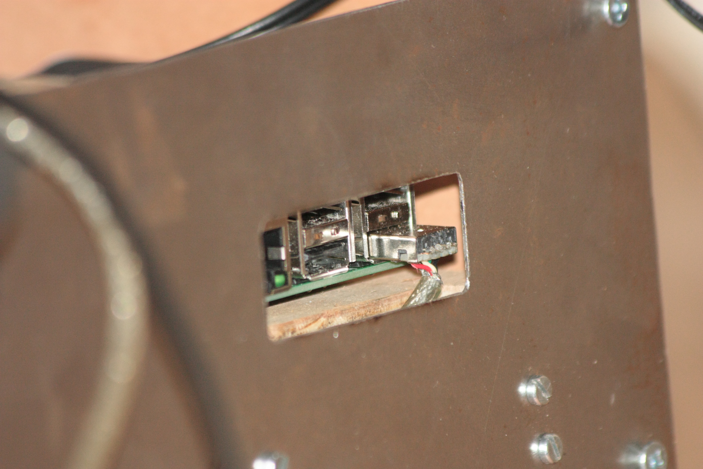
doc/v1/building-instructions/usb-cable-plugged2.jpg
