EleonoreMizo/pedalevite/doc/v1/user-manual/panel-rear.png

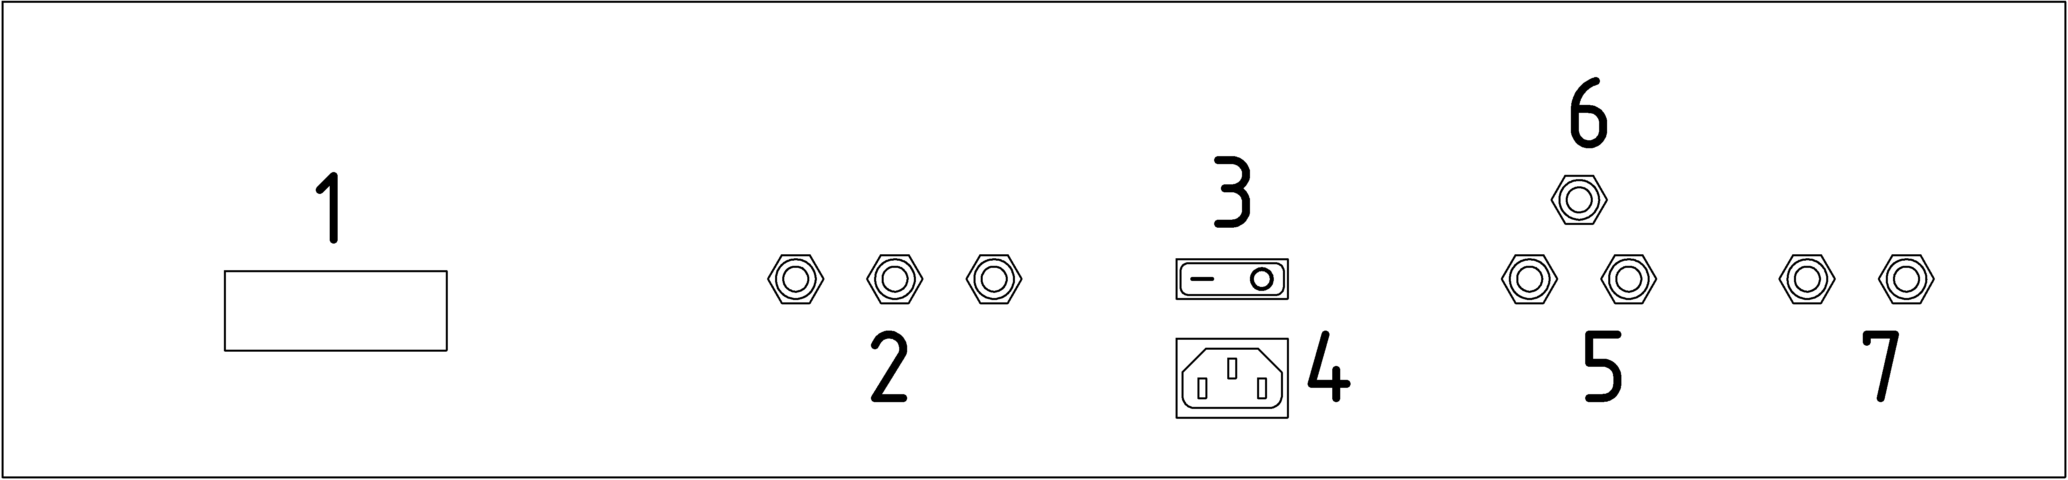
doc/v1/user-manual/panel-rear.png
