EleonoreMizo/pedalevite/src/mfx/pi/lipid/LipidipiDesc.h

/*****************************************************************************

        LipidipiDesc.h
        Author: Laurent de Soras, 2021

--- Legal stuff ---

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
*Tab=3***********************************************************************/



#pragma once
#if ! defined (mfx_pi_lipid_LipidipiDesc_HEADER_INCLUDED)
#define mfx_pi_lipid_LipidipiDesc_HEADER_INCLUDED



/*\\\ INCLUDE FILES \\\\\\\\\\\\\\\\\\\\\\\\\\\\\\\\\\\\\\\\\\\\\\\\\\\\\\\\*/

#include "mfx/pi/ParamDescSet.h"
#include "mfx/piapi/PluginDescInterface.h"



namespace mfx
{
namespace pi
{
namespace lipid
{



class LipidipiDesc final
:	public piapi::PluginDescInterface
{

/*\\\ PUBLIC \\\\\\\\\\\\\\\\\\\\\\\\\\\\\\\\\\\\\\\\\\\\\\\\\\\\\\\\\\\\\\\*/

public:

	explicit       LipidipiDesc ();
	               ~LipidipiDesc () = default;

	ParamDescSet & use_desc_set ();



/*\\\ PROTECTED \\\\\\\\\\\\\\\\\\\\\\\\\\\\\\\\\\\\\\\\\\\\\\\\\\\\\\\\\\\\*/

protected:

	// mfx::piapi::PluginDescInterface
	piapi::PluginInfo
	               do_get_info () const final;
	void           do_get_nbr_io (int &nbr_i, int &nbr_o, int &nbr_s) const final;
	int            do_get_nbr_param (piapi::ParamCateg categ) const final;
	const piapi::ParamDescInterface &
	               do_get_param_info (piapi::ParamCateg categ, int index) const final;



/*\\\ PRIVATE \\\\\\\\\\\\\\\\\\\\\\\\\\\\\\\\\\\\\\\\\\\\\\\\\\\\\\\\\\\\\\*/

private:

	ParamDescSet   _desc_set;
	piapi::PluginInfo
	               _info;



/*\\\ FORBIDDEN MEMBER FUNCTIONS \\\\\\\\\\\\\\\\\\\\\\\\\\\\\\\\\\\\\\\\\\\*/

private:

	               LipidipiDesc (const LipidipiDesc &other)      = delete;
	               LipidipiDesc (LipidipiDesc &&other)           = delete;
	LipidipiDesc & operator = (const LipidipiDesc &other)        = delete;
	LipidipiDesc & operator = (LipidipiDesc &&other)             = delete;
	bool           operator == (const LipidipiDesc &other) const = delete;
	bool           operator != (const LipidipiDesc &other) const = delete;

}; // class LipidipiDesc



}  // namespace lipid
}  // namespace pi
}  // namespace mfx



//#include "mfx/pi/lipid/LipidipiDesc.hpp"



#endif   // mfx_pi_lipid_LipidipiDesc_HEADER_INCLUDED



/*\\\ EOF \\\\\\\\\\\\\\\\\\\\\\\\\\\\\\\\\\\\\\\\\\\\\\\\\\\\\\\\\\\\\\\\\\*/
