EleonoreMizo/pedalevite/src/mfx/dsp/osc/SweepingSin.h

/*****************************************************************************

        SweepingSin.h
        Author: Laurent de Soras, 2019

--- Legal stuff ---

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
*Tab=3***********************************************************************/



#pragma once
#if ! defined (mfx_dsp_osc_SweepingSin_HEADER_INCLUDED)
#define mfx_dsp_osc_SweepingSin_HEADER_INCLUDED

#if defined (_MSC_VER)
	#pragma warning (4 : 4250)
#endif



/*\\\ INCLUDE FILES \\\\\\\\\\\\\\\\\\\\\\\\\\\\\\\\\\\\\\\\\\\\\\\\\\\\\\\\*/



namespace mfx
{
namespace dsp
{
namespace osc
{



class SweepingSin
{

/*\\\ PUBLIC \\\\\\\\\\\\\\\\\\\\\\\\\\\\\\\\\\\\\\\\\\\\\\\\\\\\\\\\\\\\\\\*/

public:

	               SweepingSin ()                         = default;
	explicit       SweepingSin (double fs, double f1, double f2) noexcept;
	               SweepingSin (const SweepingSin &other) = default;
	               SweepingSin (SweepingSin &&other)      = default;

	               ~SweepingSin ()                        = default;

	SweepingSin &  operator = (const SweepingSin &other)  = default;
	SweepingSin &  operator = (SweepingSin &&other)       = default;

	void           generate (float data_ptr [], int nbr_spl) noexcept;
	void           generate (float data_ptr [], int nbr_spl, int block_start, int block_len) noexcept;



/*\\\ PROTECTED \\\\\\\\\\\\\\\\\\\\\\\\\\\\\\\\\\\\\\\\\\\\\\\\\\\\\\\\\\\\*/

protected:



/*\\\ PRIVATE \\\\\\\\\\\\\\\\\\\\\\\\\\\\\\\\\\\\\\\\\\\\\\\\\\\\\\\\\\\\\\*/

private:

	double         _fs = 44100.0;   // Hz
	double         _f1 =    20.0;   // Hz, ]0 ; _f2[
	double         _f2 = 20000.0;   // Hz, ]f1 ; fs * 0.5[



/*\\\ FORBIDDEN MEMBER FUNCTIONS \\\\\\\\\\\\\\\\\\\\\\\\\\\\\\\\\\\\\\\\\\\*/

private:

	bool           operator == (const SweepingSin &other) const = delete;
	bool           operator != (const SweepingSin &other) const = delete;

}; // class SweepingSin



}  // namespace osc
}  // namespace dsp
}  // namespace mfx



//#include "mfx/dsp/osc/SweepingSin.hpp"



#endif   // mfx_dsp_osc_SweepingSin_HEADER_INCLUDED



/*\\\ EOF \\\\\\\\\\\\\\\\\\\\\\\\\\\\\\\\\\\\\\\\\\\\\\\\\\\\\\\\\\\\\\\\\\*/
