EleonoreMizo/pedalevite/src/fstb/Vs32.h

/*****************************************************************************

        Vs32.h
        Author: Laurent de Soras, 2021

--- Legal stuff ---

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
*Tab=3***********************************************************************/



#pragma once
#if ! defined (fstb_Vs32_HEADER_INCLUDED)
#define fstb_Vs32_HEADER_INCLUDED



/*\\\ INCLUDE FILES \\\\\\\\\\\\\\\\\\\\\\\\\\\\\\\\\\\\\\\\\\\\\\\\\\\\\\\\*/

#include "fstb/def.h"

#if ! defined (fstb_HAS_SIMD)
	#include <array>
#elif (fstb_ARCHI == fstb_ARCHI_X86)
	#include <emmintrin.h>
#elif (fstb_ARCHI == fstb_ARCHI_ARM)
	#include <arm_neon.h>
#else
	#error
#endif

#include <tuple>

#include <cstdint>



namespace fstb
{



#if ! defined (fstb_HAS_SIMD)

typedef std::array <int32_t, 4> Vs32Native;

#elif fstb_ARCHI == fstb_ARCHI_X86

typedef __m128i   Vs32Native;

#elif fstb_ARCHI == fstb_ARCHI_ARM

typedef int32x4_t Vs32Native;

#else // fstb_ARCHI
#error
#endif // fstb_ARCHI



class Vs32
{

/*\\\ PUBLIC \\\\\\\\\\\\\\\\\\\\\\\\\\\\\\\\\\\\\\\\\\\\\\\\\\\\\\\\\\\\\\\*/

public:

	static constexpr int _len_l2 = 2;
	static constexpr int _length = 1 << _len_l2;
	typedef int32_t Scalar;

	               Vs32 ()                        = default;
   fstb_FORCEINLINE
	               Vs32 (Vs32Native a) noexcept : _x { a } {}
   explicit fstb_FORCEINLINE
	               Vs32 (Scalar a) noexcept;
	explicit fstb_FORCEINLINE
	               Vs32 (Scalar a0, Scalar a1, Scalar a2, Scalar a3) noexcept;
	explicit fstb_FORCEINLINE
	               Vs32 (const std::tuple <Scalar, Scalar, Scalar, Scalar> &a) noexcept;
	               Vs32 (const Vs32 &other)       = default;
	               Vs32 (Vs32 &&other)            = default;
	               ~Vs32 ()                       = default;
	Vs32 &         operator = (const Vs32 &other) = default;
	Vs32 &         operator = (Vs32 &&other)      = default;

	template <typename MEM>
	fstb_FORCEINLINE void
	               store (MEM *ptr) const noexcept;
	template <typename MEM>
	fstb_FORCEINLINE void
	               storeu (MEM *ptr) const noexcept;
	template <typename MEM>
	fstb_FORCEINLINE void
	               storeu_part (MEM *ptr, int n) const noexcept;

	fstb_FORCEINLINE
	               operator Vs32Native () const noexcept { return _x; }
	fstb_FORCEINLINE explicit
	               operator bool () const noexcept;

	fstb_FORCEINLINE Vs32 &
	               operator += (const Vs32Native &other) noexcept;
	fstb_FORCEINLINE Vs32 &
	               operator -= (const Vs32Native &other) noexcept;
	fstb_FORCEINLINE Vs32 &
	               operator *= (const Vs32Native &other) noexcept;

	fstb_FORCEINLINE Vs32 &
	               operator &= (const Vs32Native &other) noexcept;
	fstb_FORCEINLINE Vs32 &
	               operator |= (const Vs32Native &other) noexcept;
	fstb_FORCEINLINE Vs32 &
	               operator ^= (const Vs32Native &other) noexcept;

	fstb_FORCEINLINE Vs32 &
	               operator <<= (int imm) noexcept;
	fstb_FORCEINLINE Vs32 &
	               operator >>= (int imm) noexcept;

	fstb_FORCEINLINE Vs32
	               operator - () const noexcept;
	fstb_FORCEINLINE Vs32
	               operator ~ () const noexcept;
	fstb_FORCEINLINE Vs32
	               is_lt_0 () const noexcept;
	fstb_FORCEINLINE Vs32
	               reverse () const noexcept;

	template <int SHIFT>
	fstb_FORCEINLINE Vs32
	               rotate () const noexcept;
	template <int POS>
	fstb_FORCEINLINE int32_t
	               extract () const noexcept;
	template <int POS>
	fstb_FORCEINLINE Vs32
	               insert (int32_t val) const noexcept;
	template <int POS>
	fstb_FORCEINLINE Vs32
	               spread () const noexcept;

	fstb_FORCEINLINE std::tuple <int32_t, int32_t, int32_t, int32_t>
	               explode () const noexcept;

	fstb_FORCEINLINE int32_t
	               sum_h () const noexcept;
	fstb_FORCEINLINE int32_t
	               min_h () const noexcept;
	fstb_FORCEINLINE int32_t
	               max_h () const noexcept;

	fstb_FORCEINLINE bool
	               and_h () const noexcept;
	fstb_FORCEINLINE bool
	               or_h () const noexcept;
	fstb_FORCEINLINE unsigned int
	               movemask () const noexcept;
	fstb_FORCEINLINE int
	               count_bits () const noexcept;

	static fstb_FORCEINLINE Vs32
	               zero () noexcept;
	static fstb_FORCEINLINE Vs32
	               all1 () noexcept;
	static fstb_FORCEINLINE Vs32
	               set_mask (bool m0, bool m1, bool m2, bool m3) noexcept;
	template <int POS>
	static fstb_FORCEINLINE Vs32
	               compose (Vs32 a, Vs32 b) noexcept;

	template <typename MEM>
	static fstb_FORCEINLINE Vs32
	               load (const MEM *ptr) noexcept;
	template <typename MEM>
	static fstb_FORCEINLINE Vs32
	               loadu (const MEM *ptr) noexcept;



/*\\\ PROTECTED \\\\\\\\\\\\\\\\\\\\\\\\\\\\\\\\\\\\\\\\\\\\\\\\\\\\\\\\\\\\*/

protected:



/*\\\ PRIVATE \\\\\\\\\\\\\\\\\\\\\\\\\\\\\\\\\\\\\\\\\\\\\\\\\\\\\\\\\\\\\\*/

private:

#if ! defined (fstb_HAS_SIMD)
public:
#endif
	Vs32Native  _x;
private:



/*\\\ FORBIDDEN MEMBER FUNCTIONS \\\\\\\\\\\\\\\\\\\\\\\\\\\\\\\\\\\\\\\\\\\*/

private:

}; // class Vs32



/*\\\ GLOBAL OPERATORS AND FUNCTIONS \\\\\\\\\\\\\\\\\\\\\\\\\\\\\\\\\\\\\\\*/



fstb_FORCEINLINE Vs32 operator + (Vs32 lhs, const Vs32 &rhs) noexcept;
fstb_FORCEINLINE Vs32 operator - (Vs32 lhs, const Vs32 &rhs) noexcept;
fstb_FORCEINLINE Vs32 operator * (Vs32 lhs, const Vs32 &rhs) noexcept;
fstb_FORCEINLINE Vs32 operator & (Vs32 lhs, const Vs32 &rhs) noexcept;
fstb_FORCEINLINE Vs32 operator | (Vs32 lhs, const Vs32 &rhs) noexcept;
fstb_FORCEINLINE Vs32 operator ^ (Vs32 lhs, const Vs32 &rhs) noexcept;

template <typename T>
fstb_FORCEINLINE Vs32 operator << (Vs32 lhs, T rhs) noexcept;
template <typename T>
fstb_FORCEINLINE Vs32 operator >> (Vs32 lhs, T rhs) noexcept;

fstb_FORCEINLINE Vs32 operator == (const Vs32 &lhs, const Vs32 &rhs) noexcept;
fstb_FORCEINLINE Vs32 operator != (const Vs32 &lhs, const Vs32 &rhs) noexcept;
fstb_FORCEINLINE Vs32 operator <  (const Vs32 &lhs, const Vs32 &rhs) noexcept;
fstb_FORCEINLINE Vs32 operator <= (const Vs32 &lhs, const Vs32 &rhs) noexcept;
fstb_FORCEINLINE Vs32 operator >  (const Vs32 &lhs, const Vs32 &rhs) noexcept;
fstb_FORCEINLINE Vs32 operator >= (const Vs32 &lhs, const Vs32 &rhs) noexcept;

fstb_FORCEINLINE Vs32 abs (const Vs32 &v) noexcept;
fstb_FORCEINLINE Vs32 min (const Vs32 &lhs, const Vs32 &rhs) noexcept;
fstb_FORCEINLINE Vs32 max (const Vs32 &lhs, const Vs32 &rhs) noexcept;
fstb_FORCEINLINE Vs32 limit (const Vs32 &v, const Vs32 &mi, const Vs32 &ma) noexcept;
fstb_FORCEINLINE Vs32 select (const Vs32 &cond, const Vs32 &v_t, const Vs32 &v_f) noexcept;
fstb_FORCEINLINE std::tuple <Vs32, Vs32> swap_if (const Vs32 &cond, Vs32 lhs, Vs32 rhs) noexcept;



}  // namespace fstb



#include "fstb/Vs32.hpp"



#endif   // fstb_Vs32_HEADER_INCLUDED



/*\\\ EOF \\\\\\\\\\\\\\\\\\\\\\\\\\\\\\\\\\\\\\\\\\\\\\\\\\\\\\\\\\\\\\\\\\*/
