EleonoreMizo/pedalevite/src/fstb/FixedPoint.h

/*****************************************************************************

        FixedPoint.h
        Author: Laurent de Soras, 2016

--- Legal stuff ---

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
*Tab=3***********************************************************************/



#pragma once
#if ! defined (fstb_FixedPoint_HEADER_INCLUDED)
#define fstb_FixedPoint_HEADER_INCLUDED

#if defined (_MSC_VER)
	#pragma warning (4 : 4250)
#endif



/*\\\ INCLUDE FILES \\\\\\\\\\\\\\\\\\\\\\\\\\\\\\\\\\\\\\\\\\\\\\\\\\\\\\\\*/

#include "fstb/def.h"

#include <cstdint>



namespace fstb
{



class FixedPoint
{

/*\\\ PUBLIC \\\\\\\\\\\\\\\\\\\\\\\\\\\\\\\\\\\\\\\\\\\\\\\\\\\\\\\\\\\\\\\*/

public:

	enum class NoInit
	{
		NO = 0
	};

	inline         FixedPoint () noexcept;
	               FixedPoint (const FixedPoint &other) = default;
	inline explicit
	               FixedPoint (int32_t int_val) noexcept;
	inline explicit
	               FixedPoint (int32_t int_val, uint32_t frac_val) noexcept;
	inline explicit
	               FixedPoint (double val) noexcept;
	inline explicit
	               FixedPoint (NoInit dummy) noexcept;

	FixedPoint &   operator = (const FixedPoint &other) = default;

	inline constexpr void
	               clear () noexcept;
	inline void    set_val (double val) noexcept;
	inline constexpr void
		            set_val (int32_t int_val, uint32_t frac_val) noexcept;
	inline constexpr void
		            set_val_int64 (int64_t val) noexcept;
	inline constexpr double
		            get_val_dbl () const noexcept;
	inline constexpr float
		            get_val_flt () const noexcept;
	inline constexpr int64_t
	               get_val_int64 () const noexcept;

	inline constexpr void
	               set_int_val (int32_t int_val) noexcept;
	inline constexpr int32_t
	               get_int_val () const noexcept;
	inline constexpr int32_t
	               get_round () const noexcept;
	inline constexpr int32_t
	               get_ceil () const noexcept;
	inline constexpr void
	               set_frac_val (uint32_t frac_val) noexcept;
	inline constexpr uint32_t
	               get_frac_val () const noexcept;
	inline constexpr double
	               get_frac_val_dbl () const noexcept;
	inline constexpr float
	               get_frac_val_flt () const noexcept;

	inline constexpr void
	               neg () noexcept;
	inline constexpr void
	               abs () noexcept;

	inline constexpr void
	               bound (int32_t len) noexcept;
	inline constexpr void
	               bound_positive (int32_t len) noexcept;
	inline constexpr void
	               bound_and (int32_t and_val) noexcept;

	inline constexpr void
	               add (const FixedPoint &val) noexcept;
	inline constexpr void
	               add (const FixedPoint &val, int32_t and_val) noexcept;
	inline constexpr void
	               add_int (int32_t int_val) noexcept;
	inline constexpr void
	               add_int (int32_t int_val, int32_t and_val) noexcept;
	inline constexpr void
	               add_frac (uint32_t frac_val) noexcept;
	inline constexpr void
	               add_frac (uint32_t frac_val, int32_t and_val) noexcept;
	inline constexpr FixedPoint &
	               operator += (const FixedPoint &other) noexcept;
	inline constexpr FixedPoint &
	               operator += (int32_t int_val) noexcept;

	inline constexpr void
	               sub (const FixedPoint &val) noexcept;
	inline constexpr void
	               sub (const FixedPoint &val, int32_t and_val) noexcept;
	inline constexpr void
	               sub_int (int32_t int_val) noexcept;
	inline constexpr void
	               sub_int (int32_t int_val, int32_t and_val) noexcept;
	inline constexpr void
	               sub_frac (uint32_t frac_val) noexcept;
	inline constexpr void
	               sub_frac (uint32_t frac_val, int32_t and_val) noexcept;
	inline constexpr FixedPoint &
	               operator -= (const FixedPoint &other) noexcept;
	inline constexpr FixedPoint &
	               operator -= (int32_t int_val) noexcept;

	inline constexpr void
	               shift (int nbr_bits) noexcept;
	inline constexpr void
	               shift_left (int nbr_bits) noexcept;
	inline constexpr void
	               shift_right (int nbr_bits) noexcept;
	inline constexpr FixedPoint &
	               operator <<= (int nbr_bits) noexcept;
	inline constexpr FixedPoint &
	               operator >>= (int nbr_bits) noexcept;

	inline constexpr void
	               mul_int (int32_t val) noexcept;
	inline void    mul_flt (double val) noexcept;



/*\\\ PROTECTED \\\\\\\\\\\\\\\\\\\\\\\\\\\\\\\\\\\\\\\\\\\\\\\\\\\\\\\\\\\\*/

protected:



/*\\\ PRIVATE \\\\\\\\\\\\\\\\\\\\\\\\\\\\\\\\\\\\\\\\\\\\\\\\\\\\\\\\\\\\\\*/

private:

	union Fixed3232
	{
	public:
		int64_t        _all;
		struct
		{
#if fstb_ENDIAN == fstb_ENDIAN_BIG
			int32_t        _msw;
			uint32_t       _lsw;
#else
			uint32_t       _lsw;
			int32_t	      _msw;
#endif
		}              _part;
	};

	Fixed3232      _val;

	friend bool	operator == (const FixedPoint &left, const FixedPoint &right) noexcept; 
	friend bool	operator != (const FixedPoint &left, const FixedPoint &right) noexcept; 
	friend bool	operator < (const FixedPoint &left, const FixedPoint &right) noexcept; 
	friend bool	operator <= (const FixedPoint &left, const FixedPoint &right) noexcept; 
	friend bool	operator > (const FixedPoint &left, const FixedPoint &right) noexcept; 
	friend bool	operator >= (const FixedPoint &left, const FixedPoint &right) noexcept; 



/*\\\ FORBIDDEN MEMBER FUNCTIONS \\\\\\\\\\\\\\\\\\\\\\\\\\\\\\\\\\\\\\\\\\\*/

private:

}; // class FixedPoint



/*\\\ GLOBAL OPERATOR PROTOTYPES \\\\\\\\\\\\\\\\\\\\\\\\\\\\\\\\\\\\\\\\\\\*/

inline bool	operator == (const FixedPoint &left, const FixedPoint &right) noexcept; 
inline bool	operator != (const FixedPoint &left, const FixedPoint &right) noexcept; 
inline bool	operator < (const FixedPoint &left, const FixedPoint &right) noexcept; 
inline bool	operator <= (const FixedPoint &left, const FixedPoint &right) noexcept; 
inline bool	operator > (const FixedPoint &left, const FixedPoint &right) noexcept; 
inline bool	operator >= (const FixedPoint &left, const FixedPoint &right) noexcept; 

inline FixedPoint	operator + (FixedPoint left, const FixedPoint &right) noexcept;
inline FixedPoint	operator - (FixedPoint left, const FixedPoint &right) noexcept;
inline FixedPoint operator * (FixedPoint left, int32_t right) noexcept;
inline FixedPoint operator * (FixedPoint left, double right) noexcept;



}  // namespace fstb



#include "fstb/FixedPoint.hpp"



#endif   // fstb_FixedPoint_HEADER_INCLUDED



/*\\\ EOF \\\\\\\\\\\\\\\\\\\\\\\\\\\\\\\\\\\\\\\\\\\\\\\\\\\\\\\\\\\\\\\\\\*/
