EleonoreMizo/pedalevite/src/fstb/Poly.h

/*****************************************************************************

        Poly.h
        Author: Laurent de Soras, 2021

--- Legal stuff ---

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
*Tab=3***********************************************************************/



#pragma once
#if ! defined (fstb_Poly_HEADER_INCLUDED)
#define fstb_Poly_HEADER_INCLUDED



/*\\\ INCLUDE FILES \\\\\\\\\\\\\\\\\\\\\\\\\\\\\\\\\\\\\\\\\\\\\\\\\\\\\\\\*/

#include "fstb/def.h"
#include "fstb/Vf32.h"



namespace fstb
{



class Poly
{

/*\\\ PUBLIC \\\\\\\\\\\\\\\\\\\\\\\\\\\\\\\\\\\\\\\\\\\\\\\\\\\\\\\\\\\\\\\*/

public:

	template <class T>
	fstb_FORCEINLINE static constexpr T
	               horner (T x, T c0, T c1) noexcept;
	template <class T>
	fstb_FORCEINLINE static constexpr T
	               horner (T x, T c0, T c1, T c2) noexcept;
	template <class T>
	fstb_FORCEINLINE static constexpr T
	               horner (T x, T c0, T c1, T c2, T c3) noexcept;
	template <class T>
	fstb_FORCEINLINE static constexpr T
	               horner (T x, T c0, T c1, T c2, T c3, T c4) noexcept;
	template <class T>
	fstb_FORCEINLINE static constexpr T
	               horner (T x, T c0, T c1, T c2, T c3, T c4, T c5) noexcept;
	template <class T>
	fstb_FORCEINLINE static constexpr T
	               horner (T x, T c0, T c1, T c2, T c3, T c4, T c5, T c6) noexcept;
	template <class T>
	fstb_FORCEINLINE static constexpr T
	               horner (T x, T c0, T c1, T c2, T c3, T c4, T c5, T c6, T c7) noexcept;

	template <class T, int N>
	fstb_FORCEINLINE static constexpr T
	               horner (T x, const T (&c) [N]) noexcept;

	template <class T>
	fstb_FORCEINLINE static constexpr T
	               estrin (T x, T c0, T c1, T c2, T c3) noexcept;
	template <class T>
	fstb_FORCEINLINE static constexpr T
	               estrin (T x, T c0, T c1, T c2, T c3, T c4) noexcept;
	template <class T>
	fstb_FORCEINLINE static constexpr T
	               estrin (T x, T c0, T c1, T c2, T c3, T c4, T c5) noexcept;
	template <class T>
	fstb_FORCEINLINE static constexpr T
	               estrin (T x, T c0, T c1, T c2, T c3, T c4, T c5, T c6) noexcept;
	template <class T>
	fstb_FORCEINLINE static constexpr T
	               estrin (T x, T c0, T c1, T c2, T c3, T c4, T c5, T c6, T c7) noexcept;

	template <class T, int N>
	fstb_FORCEINLINE static constexpr T
	               estrin (T x, const T (&c) [N]) noexcept;



/*\\\ PROTECTED \\\\\\\\\\\\\\\\\\\\\\\\\\\\\\\\\\\\\\\\\\\\\\\\\\\\\\\\\\\\*/

protected:



/*\\\ PRIVATE \\\\\\\\\\\\\\\\\\\\\\\\\\\\\\\\\\\\\\\\\\\\\\\\\\\\\\\\\\\\\\*/

private:

	template <class T>
	fstb_FORCEINLINE static constexpr T
	               fma (T x, T a, T b) noexcept;



/*\\\ FORBIDDEN MEMBER FUNCTIONS \\\\\\\\\\\\\\\\\\\\\\\\\\\\\\\\\\\\\\\\\\\*/

private:

	               Poly ()                               = delete;
	               Poly (const Poly &other)              = delete;
	               Poly (Poly &&other)                   = delete;
	Poly &         operator = (const Poly &other)        = delete;
	Poly &         operator = (Poly &&other)             = delete;
	bool           operator == (const Poly &other) const = delete;
	bool           operator != (const Poly &other) const = delete;

}; // class Poly



}  // namespace fstb



#include "fstb/Poly.hpp"



#endif   // fstb_Poly_HEADER_INCLUDED



/*\\\ EOF \\\\\\\\\\\\\\\\\\\\\\\\\\\\\\\\\\\\\\\\\\\\\\\\\\\\\\\\\\\\\\\\\\*/
