EleonoreMizo/pedalevite/src/fstb/Hash.h

/*****************************************************************************

        Hash.h
        Author: Laurent de Soras, 2020

Hash functions with a low bias. These hash functions are invertible.
Note: hash of 0 is still 0, for any data size.

Source: Chris Wellons
https://nullprogram.com/blog/2018/07/31/

Also: Vincent Lunot
https://lemire.me/blog/2017/09/18/computing-the-inverse-of-odd-integers/

Other hash functions. Probably invertible, but formula was not given.
They make even better peseudo-random generators when feed with a counter.

rrmxmx: Pelle Evensen,
http://mostlymangling.blogspot.com/2018/07/on-mixing-functions-in-fast-splittable.html

nasam: Pelle Evensen,
http://mostlymangling.blogspot.com/2020/01/nasam-not-another-strange-acronym-mixer.html

pelican: Tommy Ettinger, similar to nasam, but without fixed point at 0,
https://github.com/tommyettinger/sarong/blob/master/src/main/java/sarong/PelicanRNG.java

--- Legal stuff ---

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
*Tab=3***********************************************************************/



#pragma once
#if ! defined (fstb_Hash_HEADER_INCLUDED)
#define fstb_Hash_HEADER_INCLUDED



/*\\\ INCLUDE FILES \\\\\\\\\\\\\\\\\\\\\\\\\\\\\\\\\\\\\\\\\\\\\\\\\\\\\\\\*/

#include "fstb/def.h"
#include "fstb/Vu32.h"

#include <cstdint>



namespace fstb
{



class Hash
{

/*\\\ PUBLIC \\\\\\\\\\\\\\\\\\\\\\\\\\\\\\\\\\\\\\\\\\\\\\\\\\\\\\\\\\\\\\\*/

public:

	static fstb_FORCEINLINE constexpr uint32_t
	               hash (uint32_t x) noexcept;
	static fstb_FORCEINLINE Vu32
	               hash (Vu32 x) noexcept;
	static fstb_FORCEINLINE constexpr uint32_t
	               hash_inv (uint32_t x) noexcept;
	static fstb_FORCEINLINE Vu32
	               hash_inv (Vu32 x) noexcept;

	static fstb_FORCEINLINE constexpr uint64_t
	               hash (uint64_t x) noexcept;
	static fstb_FORCEINLINE constexpr uint64_t
	               hash_inv (uint64_t x) noexcept;

	static fstb_FORCEINLINE constexpr uint64_t
	               rrmxmx (uint64_t x) noexcept;
	static fstb_FORCEINLINE constexpr uint64_t
	               nasam (uint64_t x) noexcept;
	static fstb_FORCEINLINE constexpr uint64_t
	               pelican (uint64_t x) noexcept;



/*\\\ PROTECTED \\\\\\\\\\\\\\\\\\\\\\\\\\\\\\\\\\\\\\\\\\\\\\\\\\\\\\\\\\\\*/

protected:



/*\\\ PRIVATE \\\\\\\\\\\\\\\\\\\\\\\\\\\\\\\\\\\\\\\\\\\\\\\\\\\\\\\\\\\\\\*/

private:



/*\\\ FORBIDDEN MEMBER FUNCTIONS \\\\\\\\\\\\\\\\\\\\\\\\\\\\\\\\\\\\\\\\\\\*/

private:

	               Hash ()                               = delete;
	               Hash (const Hash &other)              = delete;
	               Hash (Hash &&other)                   = delete;
	               ~Hash ()                              = delete;
	Hash &         operator = (const Hash &other)        = delete;
	Hash &         operator = (Hash &&other)             = delete;
	bool           operator == (const Hash &other) const = delete;
	bool           operator != (const Hash &other) const = delete;

}; // class Hash



}  // namespace fstb



#include "fstb/Hash.hpp"



#endif   // fstb_Hash_HEADER_INCLUDED



/*\\\ EOF \\\\\\\\\\\\\\\\\\\\\\\\\\\\\\\\\\\\\\\\\\\\\\\\\\\\\\\\\\\\\\\\\\*/
