EleonoreMizo/pedalevite/src/ffft/FFTRealFixLen.h

/*****************************************************************************

        FFTRealFixLen.h
        By Laurent de Soras

--- Legal stuff ---

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
*Tab=3***********************************************************************/



#if ! defined (ffft_FFTRealFixLen_HEADER_INCLUDED)
#define	ffft_FFTRealFixLen_HEADER_INCLUDED

#if defined (_MSC_VER)
	#pragma once
	#pragma warning (4 : 4250) // "Inherits via dominance."
#endif



/*\\\ INCLUDE FILES \\\\\\\\\\\\\\\\\\\\\\\\\\\\\\\\\\\\\\\\\\\\\\\\\\\\\\\\*/

#include	"ffft/FFTRealFixLenParam.h"
#include	"ffft/OscSinCos.h"

#include <array>
#include <vector>


namespace ffft
{



template <int LL2>
class FFTRealFixLen
{
	typedef	int	CompileTimeCheck1 [(LL2 >=  0) ? 1 : -1];
	typedef	int	CompileTimeCheck2 [(LL2 <= 30) ? 1 : -1];

/*\\\ PUBLIC \\\\\\\\\\\\\\\\\\\\\\\\\\\\\\\\\\\\\\\\\\\\\\\\\\\\\\\\\\\\\\\*/

public:

   typedef	FFTRealFixLenParam::DataType   DataType;
	typedef	OscSinCos <DataType>	OscType;

	static constexpr int FFT_LEN_L2 = LL2;
	static constexpr int FFT_LEN    = 1 << FFT_LEN_L2;

						FFTRealFixLen ();
						~FFTRealFixLen ()                          = default;
						FFTRealFixLen (const FFTRealFixLen &other) = default;
						FFTRealFixLen (FFTRealFixLen &&other)      = default;

	FFTRealFixLen&	operator = (const FFTRealFixLen &other)    = default;
	FFTRealFixLen&	operator = (FFTRealFixLen &&other)         = default;

	inline long		get_length () const noexcept;
	void				do_fft (DataType f [], const DataType x []) noexcept;
	void				do_ifft (const DataType f [], DataType x []) noexcept;
	void				rescale (DataType x []) const noexcept;



/*\\\ PROTECTED \\\\\\\\\\\\\\\\\\\\\\\\\\\\\\\\\\\\\\\\\\\\\\\\\\\\\\\\\\\\*/

protected:



/*\\\ PRIVATE \\\\\\\\\\\\\\\\\\\\\\\\\\\\\\\\\\\\\\\\\\\\\\\\\\\\\\\\\\\\\\*/

private:

	static constexpr int TRIGO_BD_LIMIT = FFTRealFixLenParam::TRIGO_BD_LIMIT;

	static constexpr int BR_ARR_SIZE_L2 =
		((FFT_LEN_L2 - 3) < 0) ? 0 : (FFT_LEN_L2 - 2);
	static constexpr int BR_ARR_SIZE    = 1 << BR_ARR_SIZE_L2;

   static constexpr int TRIGO_BD			=
		  ((FFT_LEN_L2 - TRIGO_BD_LIMIT) < 0)
		? (int)FFT_LEN_L2
		: (int)TRIGO_BD_LIMIT;
	static constexpr int TRIGO_TABLE_ARR_SIZE_L2 =
		(LL2 < 4) ? 0 : (TRIGO_BD - 2);
	static constexpr int TRIGO_TABLE_ARR_SIZE    =
		1 << TRIGO_TABLE_ARR_SIZE_L2;

	static constexpr int NBR_TRIGO_OSC      = FFT_LEN_L2 - TRIGO_BD;
	static constexpr int TRIGO_OSC_ARR_SIZE =
		(NBR_TRIGO_OSC > 0) ? NBR_TRIGO_OSC : 1;

	void				build_br_lut () noexcept;
	void				build_trigo_lut () noexcept;
	void				build_trigo_osc () noexcept;

	std::vector <DataType>
						_buffer;
	std::vector <long>
						_br_data;
	std::vector <DataType>
						_trigo_data;
   std::array <OscType, TRIGO_OSC_ARR_SIZE>
						_trigo_osc;



/*\\\ FORBIDDEN MEMBER FUNCTIONS \\\\\\\\\\\\\\\\\\\\\\\\\\\\\\\\\\\\\\\\\\\*/

private:

	bool				operator == (const FFTRealFixLen &other) = delete;
	bool				operator != (const FFTRealFixLen &other) = delete;

};	// class FFTRealFixLen



}	// namespace ffft



#include	"ffft/FFTRealFixLen.hpp"



#endif	// ffft_FFTRealFixLen_HEADER_INCLUDED



/*\\\ EOF \\\\\\\\\\\\\\\\\\\\\\\\\\\\\\\\\\\\\\\\\\\\\\\\\\\\\\\\\\\\\\\\\\*/
