EleonoreMizo/pedalevite/src/mfx/hw/GpioAccess.hpp

/*****************************************************************************

        GpioAccess.hpp
        Author: Laurent de Soras, 2019

--- Legal stuff ---

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
*Tab=3***********************************************************************/



#if ! defined (mfx_hw_GpioAccess_CODEHEADER_INCLUDED)
#define mfx_hw_GpioAccess_CODEHEADER_INCLUDED



/*\\\ INCLUDE FILES \\\\\\\\\\\\\\\\\\\\\\\\\\\\\\\\\\\\\\\\\\\\\\\\\\\\\\\\*/

#include <cassert>



namespace mfx
{
namespace hw
{



/*\\\ PUBLIC \\\\\\\\\\\\\\\\\\\\\\\\\\\\\\\\\\\\\\\\\\\\\\\\\\\\\\\\\\\\\\\*/



void	GpioAccess::clear (int gpio) const
{
	assert (gpio >= 0);
	assert (gpio < _nbr_gpio);

	const uint32_t mask = uint32_t (1) << gpio;
	_gpio_ptr [_reg_clr] = mask;
}



void	GpioAccess::set (int gpio) const
{
	assert (gpio >= 0);
	assert (gpio < _nbr_gpio);

	const uint32_t mask = uint32_t (1) << gpio;
	_gpio_ptr [_reg_set] = mask;
}



void	GpioAccess::write (int gpio, int val) const
{
	assert (gpio >= 0);
	assert (gpio < _nbr_gpio);

	if (val == 0)
	{
		clear (gpio);
	}
	else
	{
		set (gpio);
	}
}



int	GpioAccess::read (int gpio) const
{
	assert (gpio >= 0);
	assert (gpio < _nbr_gpio);

	return (_gpio_ptr [_reg_lvl] >> gpio) & 1;
}



/*\\\ PROTECTED \\\\\\\\\\\\\\\\\\\\\\\\\\\\\\\\\\\\\\\\\\\\\\\\\\\\\\\\\\\\*/



/*\\\ PRIVATE \\\\\\\\\\\\\\\\\\\\\\\\\\\\\\\\\\\\\\\\\\\\\\\\\\\\\\\\\\\\\\*/



void	GpioAccess::find_addr_fnc (int &ofs_reg, int &shf_bit, int gpio)
{
	assert (gpio >= 0);
	assert (gpio < _nbr_gpio);

	const int      nbr_gpio_per_reg = 10;

	ofs_reg =  gpio / nbr_gpio_per_reg;
	shf_bit =
		  (gpio - (ofs_reg * nbr_gpio_per_reg)) * bcm2837gpio::_fnc_field_size;
}



}  // namespace hw
}  // namespace mfx



#endif   // mfx_hw_GpioAccess_CODEHEADER_INCLUDED



/*\\\ EOF \\\\\\\\\\\\\\\\\\\\\\\\\\\\\\\\\\\\\\\\\\\\\\\\\\\\\\\\\\\\\\\\\\*/
