EleonoreMizo/pedalevite/src/fstb/DataAlign.h

/*****************************************************************************

        DataAlign.h
        Author: Laurent de Soras, 2016

--- Legal stuff ---

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
*Tab=3***********************************************************************/



#pragma once
#if ! defined (fstb_DataAlign_HEADER_INCLUDED)
#define fstb_DataAlign_HEADER_INCLUDED

#if defined (_MSC_VER)
	#pragma warning (4 : 4250)
#endif



/*\\\ INCLUDE FILES \\\\\\\\\\\\\\\\\\\\\\\\\\\\\\\\\\\\\\\\\\\\\\\\\\\\\\\\*/

#include "fstb/Vf32.h"
#include "fstb/Vs32.h"

#include <type_traits>



namespace fstb
{



template <bool A>
class DataAlign
{

/*\\\ PUBLIC \\\\\\\\\\\\\\\\\\\\\\\\\\\\\\\\\\\\\\\\\\\\\\\\\\\\\\\\\\\\\\\*/

public:

	typedef std::integral_constant <bool, A> Alignment;

	static inline bool
		            check_ptr (const void *ptr) noexcept;
	static inline Vf32
		            load_f32 (const void *ptr) noexcept;
	static inline Vs32
		            load_s32 (const void *ptr) noexcept;
	static inline void
		            store_f32 (void *ptr, Vf32 v) noexcept;
	static inline void
		            store_s32 (void *ptr, Vs32 v) noexcept;



/*\\\ PROTECTED \\\\\\\\\\\\\\\\\\\\\\\\\\\\\\\\\\\\\\\\\\\\\\\\\\\\\\\\\\\\*/

protected:



/*\\\ PRIVATE \\\\\\\\\\\\\\\\\\\\\\\\\\\\\\\\\\\\\\\\\\\\\\\\\\\\\\\\\\\\\\*/

private:



/*\\\ FORBIDDEN MEMBER FUNCTIONS \\\\\\\\\\\\\\\\\\\\\\\\\\\\\\\\\\\\\\\\\\\*/

private:

	               ~DataAlign ()                              = delete;
	               DataAlign ()                               = delete;
	               DataAlign (const DataAlign &other)         = delete;
	DataAlign &    operator = (const DataAlign &other)        = delete;
	bool           operator == (const DataAlign &other) const = delete;
	bool           operator != (const DataAlign &other) const = delete;

}; // class DataAlign



}  // namespace fstb



#include "fstb/DataAlign.hpp"



#endif   // fstb_DataAlign_HEADER_INCLUDED



/*\\\ EOF \\\\\\\\\\\\\\\\\\\\\\\\\\\\\\\\\\\\\\\\\\\\\\\\\\\\\\\\\\\\\\\\\\*/
