EleonoreMizo/pedalevite/src/ffft/FFTRealUseTrigo.hpp

/*****************************************************************************

        FFTRealUseTrigo.hpp
        By Laurent de Soras

--- Legal stuff ---

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
*Tab=3***********************************************************************/



#if defined (ffft_FFTRealUseTrigo_CURRENT_CODEHEADER)
	#error Recursive inclusion of FFTRealUseTrigo code header.
#endif
#define	ffft_FFTRealUseTrigo_CURRENT_CODEHEADER

#if ! defined (ffft_FFTRealUseTrigo_CODEHEADER_INCLUDED)
#define	ffft_FFTRealUseTrigo_CODEHEADER_INCLUDED



/*\\\ INCLUDE FILES \\\\\\\\\\\\\\\\\\\\\\\\\\\\\\\\\\\\\\\\\\\\\\\\\\\\\\\\*/

#include	"ffft/OscSinCos.h"



namespace ffft
{



/*\\\ PUBLIC \\\\\\\\\\\\\\\\\\\\\\\\\\\\\\\\\\\\\\\\\\\\\\\\\\\\\\\\\\\\\\\*/



template <int ALGO>
void	FFTRealUseTrigo <ALGO>::prepare (OscType &osc) noexcept
{
	osc.clear_buffers ();
}

template <>
inline void	FFTRealUseTrigo <0>::prepare (OscType &/*osc*/) noexcept
{
	// Nothing
}



template <int ALGO>
void	FFTRealUseTrigo <ALGO>::iterate (OscType &osc, DataType &c, DataType &s, const DataType /*cos_ptr*/ [], long /*index_c*/, long /*index_s*/) noexcept
{
	osc.step ();
	c = osc.get_cos ();
	s = osc.get_sin ();
}

template <>
inline void	FFTRealUseTrigo <0>::iterate (OscType &/*osc*/, DataType &c, DataType &s, const DataType cos_ptr [], long index_c, long index_s) noexcept
{
	c = cos_ptr [index_c];
	s = cos_ptr [index_s];
}



/*\\\ PROTECTED \\\\\\\\\\\\\\\\\\\\\\\\\\\\\\\\\\\\\\\\\\\\\\\\\\\\\\\\\\\\*/



/*\\\ PRIVATE \\\\\\\\\\\\\\\\\\\\\\\\\\\\\\\\\\\\\\\\\\\\\\\\\\\\\\\\\\\\\\*/



}	// namespace ffft



#endif	// ffft_FFTRealUseTrigo_CODEHEADER_INCLUDED

#undef ffft_FFTRealUseTrigo_CURRENT_CODEHEADER



/*\\\ EOF \\\\\\\\\\\\\\\\\\\\\\\\\\\\\\\\\\\\\\\\\\\\\\\\\\\\\\\\\\\\\\\\\\*/
