EleonoreMizo/pedalevite/src/ffft/OscSinCos.hpp

/*****************************************************************************

        OscSinCos.hpp
        By Laurent de Soras

--- Legal stuff ---

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
*Tab=3***********************************************************************/



#if defined (ffft_OscSinCos_CURRENT_CODEHEADER)
	#error Recursive inclusion of OscSinCos code header.
#endif
#define	ffft_OscSinCos_CURRENT_CODEHEADER

#if ! defined (ffft_OscSinCos_CODEHEADER_INCLUDED)
#define	ffft_OscSinCos_CODEHEADER_INCLUDED



/*\\\ INCLUDE FILES \\\\\\\\\\\\\\\\\\\\\\\\\\\\\\\\\\\\\\\\\\\\\\\\\\\\\\\\*/

#include	<cmath>

namespace std { }



namespace ffft
{



/*\\\ PUBLIC \\\\\\\\\\\\\\\\\\\\\\\\\\\\\\\\\\\\\\\\\\\\\\\\\\\\\\\\\\\\\\\*/



template <class T>
void	OscSinCos <T>::set_step (double angle_rad) noexcept
{
	_step_cos = static_cast <DataType> (cos (angle_rad));
	_step_sin = static_cast <DataType> (sin (angle_rad));
}



template <class T>
typename OscSinCos <T>::DataType	OscSinCos <T>::get_cos () const noexcept
{
	return (_pos_cos);
}



template <class T>
typename OscSinCos <T>::DataType	OscSinCos <T>::get_sin () const noexcept
{
	return (_pos_sin);
}



template <class T>
void	OscSinCos <T>::step () noexcept
{
	const DataType	old_cos = _pos_cos;
	const DataType	old_sin = _pos_sin;

	_pos_cos = old_cos * _step_cos - old_sin * _step_sin;
	_pos_sin = old_cos * _step_sin + old_sin * _step_cos;
}



template <class T>
void	OscSinCos <T>::clear_buffers () noexcept
{
	_pos_cos = static_cast <DataType> (1);
	_pos_sin = static_cast <DataType> (0);
}



/*\\\ PROTECTED \\\\\\\\\\\\\\\\\\\\\\\\\\\\\\\\\\\\\\\\\\\\\\\\\\\\\\\\\\\\*/



/*\\\ PRIVATE \\\\\\\\\\\\\\\\\\\\\\\\\\\\\\\\\\\\\\\\\\\\\\\\\\\\\\\\\\\\\\*/



}	// namespace ffft



#endif	// ffft_OscSinCos_CODEHEADER_INCLUDED

#undef ffft_OscSinCos_CURRENT_CODEHEADER



/*\\\ EOF \\\\\\\\\\\\\\\\\\\\\\\\\\\\\\\\\\\\\\\\\\\\\\\\\\\\\\\\\\\\\\\\\\*/
