EleonoreMizo/pedalevite/src/fstb/BitFieldSparse.h

/*****************************************************************************

        BitFieldSparse.h
        Author: Laurent de Soras, 2006

--- Legal stuff ---

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
*Tab=3***********************************************************************/



#pragma once
#if ! defined (fstb_BitFieldSparse_HEADER_INCLUDED)
#define fstb_BitFieldSparse_HEADER_INCLUDED

#if defined (_MSC_VER)
	#pragma warning (4 : 4250)
#endif



/*\\\ INCLUDE FILES \\\\\\\\\\\\\\\\\\\\\\\\\\\\\\\\\\\\\\\\\\\\\\\\\\\\\\\\*/

#include <vector>

#include <cstdint>



namespace fstb
{



class BitFieldSparse
{

/*\\\ PUBLIC \\\\\\\\\\\\\\\\\\\\\\\\\\\\\\\\\\\\\\\\\\\\\\\\\\\\\\\\\\\\\\\*/

public:


	               BitFieldSparse ();
	explicit       BitFieldSparse (int nbr_elt);
	               BitFieldSparse (const BitFieldSparse &other) = default;

	BitFieldSparse &
	               operator = (const BitFieldSparse &other)     = default;

	void           set_nbr_elt (int nbr_elt);
	int            get_nbr_elt () const noexcept;
	void           clear () noexcept;
	void           fill () noexcept;

   bool           get_bit (int pos) const noexcept;
   void           set_bit (int pos, bool flag) noexcept;
   void           clear_bit (int pos) noexcept;
   void           fill_bit (int pos) noexcept;

   void           activate_range (int pos, int nbr_elt) noexcept;
   void           deactivate_range (int pos, int nbr_elt) noexcept;

   int            get_next_bit_set_from (int pos, int stop_pos = -1) const noexcept;
	bool           has_a_bit_set () const noexcept;



/*\\\ PROTECTED \\\\\\\\\\\\\\\\\\\\\\\\\\\\\\\\\\\\\\\\\\\\\\\\\\\\\\\\\\\\*/

protected:



/*\\\ PRIVATE \\\\\\\\\\\\\\\\\\\\\\\\\\\\\\\\\\\\\\\\\\\\\\\\\\\\\\\\\\\\\\*/

private:

   static constexpr int BITDEPTH_L2 = 5;  // 32 bits
   static constexpr int BITDEPTH    = 1 << BITDEPTH_L2;

	typedef	uint32_t	GroupType;

	class BfLevel
	{
	public:
		typedef std::vector <GroupType> GroupArray;
		GroupArray     _group_arr;
		int            _nbr_elt = 0;
	};

	typedef std::vector <BfLevel> LevelArray;

	int            get_next_bit_set_from_rec (int lvl_index, int start, int stop) const noexcept;

	LevelArray     _lvl_arr;



/*\\\ FORBIDDEN MEMBER FUNCTIONS \\\\\\\\\\\\\\\\\\\\\\\\\\\\\\\\\\\\\\\\\\\*/

private:

	bool           operator == (const BitFieldSparse &other) const = delete;
	bool           operator != (const BitFieldSparse &other) const = delete;

}; // class BitFieldSparse



}  // namespace fstb



//#include "fstb/BitFieldSparse.hpp"



#endif   // fstb_BitFieldSparse_HEADER_INCLUDED



/*\\\ EOF \\\\\\\\\\\\\\\\\\\\\\\\\\\\\\\\\\\\\\\\\\\\\\\\\\\\\\\\\\\\\\\\\\*/
