EleonoreMizo/pedalevite/src/fstb/BitFieldSparseIterator.hpp

/*****************************************************************************

        BitFieldSparseIterator.hpp
        Author: Laurent de Soras, 2008

--- Legal stuff ---

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
*Tab=3***********************************************************************/



#if ! defined (fstb_BitFieldSparseIterator_CODEHEADER_INCLUDED)
#define fstb_BitFieldSparseIterator_CODEHEADER_INCLUDED



/*\\\ INCLUDE FILES \\\\\\\\\\\\\\\\\\\\\\\\\\\\\\\\\\\\\\\\\\\\\\\\\\\\\\\\*/

#include "fstb/BitFieldSparse.h"

#include <cassert>



namespace fstb
{



/*\\\ PUBLIC \\\\\\\\\\\\\\\\\\\\\\\\\\\\\\\\\\\\\\\\\\\\\\\\\\\\\\\\\\\\\\\*/



BitFieldSparseIterator::BitFieldSparseIterator (const BitFieldSparse &bfs) noexcept
:	_bfs (bfs)
{
	// Nothing
}



void	BitFieldSparseIterator::start (int pos_start, int pos_end) noexcept
{
	assert (pos_start >= 0);
	assert (pos_end < _bfs.get_nbr_elt ());

	if (pos_end < 0)
	{
		_pos_end = _bfs.get_nbr_elt ();
	}
	else
	{
		_pos_end = pos_end;
	}

	if (pos_start >= _pos_end)
	{
		_bit_index = -1;
	}
	else
	{
		_bit_index = _bfs.get_next_bit_set_from (pos_start, _pos_end);
	}
}



bool	BitFieldSparseIterator::is_rem_elt () const noexcept
{
	return (_bit_index >= 0);
}



void	BitFieldSparseIterator::iterate () noexcept
{
	assert (is_rem_elt ());

	const int      new_pos = _bit_index + 1;
	if (new_pos >= _pos_end)
	{
		_bit_index = -1;
	}
	else
	{
		_bit_index = _bfs.get_next_bit_set_from (new_pos, _pos_end);
	}
}



int	BitFieldSparseIterator::get_bit_index () const noexcept
{
	return _bit_index;
}



/*\\\ PROTECTED \\\\\\\\\\\\\\\\\\\\\\\\\\\\\\\\\\\\\\\\\\\\\\\\\\\\\\\\\\\\*/



/*\\\ PRIVATE \\\\\\\\\\\\\\\\\\\\\\\\\\\\\\\\\\\\\\\\\\\\\\\\\\\\\\\\\\\\\\*/



}  // namespace fstb



#endif   // fstb_BitFieldSparseIterator_CODEHEADER_INCLUDED



/*\\\ EOF \\\\\\\\\\\\\\\\\\\\\\\\\\\\\\\\\\\\\\\\\\\\\\\\\\\\\\\\\\\\\\\\\\*/
