EleonoreMizo/pedalevite/src/fstb/SingleObj.h

/*****************************************************************************

        SingleObj.h
        Author: Laurent de Soras, 2015

--- Legal stuff ---

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
*Tab=3***********************************************************************/



#pragma once
#if ! defined (fstb_SingleObj_HEADER_INCLUDED)
#define	fstb_SingleObj_HEADER_INCLUDED

#if defined (_MSC_VER)
	#pragma warning (4 : 4250)
#endif



/*\\\ INCLUDE FILES \\\\\\\\\\\\\\\\\\\\\\\\\\\\\\\\\\\\\\\\\\\\\\\\\\\\\\\\*/

#include "fstb/AllocAlign.h"



namespace fstb
{



template <class T, class A = AllocAlign <T, 16> >
class SingleObj
{

/*\\\ PUBLIC \\\\\\\\\\\\\\\\\\\\\\\\\\\\\\\\\\\\\\\\\\\\\\\\\\\\\\\\\\\\\\\*/

public:

	               SingleObj ();
	virtual        ~SingleObj ();

	T *            operator -> () const noexcept;
	T &            operator * () const noexcept;



/*\\\ PROTECTED \\\\\\\\\\\\\\\\\\\\\\\\\\\\\\\\\\\\\\\\\\\\\\\\\\\\\\\\\\\\*/

protected:



/*\\\ PRIVATE \\\\\\\\\\\\\\\\\\\\\\\\\\\\\\\\\\\\\\\\\\\\\\\\\\\\\\\\\\\\\\*/

private:

	A              _allo;
	T *            _obj_ptr;



/*\\\ FORBIDDEN MEMBER FUNCTIONS \\\\\\\\\\\\\\\\\\\\\\\\\\\\\\\\\\\\\\\\\\\*/

private:

	               SingleObj (const SingleObj <T, A> &other)         = delete;
	               SingleObj (const SingleObj <T, A> &&other)        = delete;
	SingleObj <T, A> &
	               operator = (const SingleObj <T, A> &other)        = delete;
	SingleObj <T, A> &
	               operator = (const SingleObj <T, A> &&other)       = delete;
	bool           operator == (const SingleObj <T, A> &other) const = delete;
	bool           operator != (const SingleObj <T, A> &other) const = delete;

};	// class SingleObj



}	// namespace fstb



#include "fstb/SingleObj.hpp"



#endif	// fstb_SingleObj_HEADER_INCLUDED



/*\\\ EOF \\\\\\\\\\\\\\\\\\\\\\\\\\\\\\\\\\\\\\\\\\\\\\\\\\\\\\\\\\\\\\\\\\*/
