EleonoreMizo/pedalevite/src/fstb/SingleObj.hpp

/*****************************************************************************

        SingleObj.hpp
        Author: Laurent de Soras, 2015

--- Legal stuff ---

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
*Tab=3***********************************************************************/



#if ! defined (fstb_SingleObj_CODEHEADER_INCLUDED)
#define	fstb_SingleObj_CODEHEADER_INCLUDED



/*\\\ INCLUDE FILES \\\\\\\\\\\\\\\\\\\\\\\\\\\\\\\\\\\\\\\\\\\\\\\\\\\\\\\\*/

#include <cassert>



namespace fstb
{



/*\\\ PUBLIC \\\\\\\\\\\\\\\\\\\\\\\\\\\\\\\\\\\\\\\\\\\\\\\\\\\\\\\\\\\\\\\*/



template <class T, class A>
SingleObj <T, A>::SingleObj ()
:	_allo ()
,	_obj_ptr (_allo.allocate (1))
{
	if (_obj_ptr == nullptr)
	{
#if defined (__cpp_exceptions) || ! defined (__GNUC__)
		throw std::bad_alloc ();
#endif
	}

#if defined (__cpp_exceptions) || ! defined (__GNUC__)
	try
#endif
	{
		new (_obj_ptr) T ();
	}
#if defined (__cpp_exceptions) || ! defined (__GNUC__)
	catch (...)
	{
		_allo.deallocate (_obj_ptr, 1);
		throw;
	}
#endif
}



template <class T, class A>
SingleObj <T, A>::~SingleObj ()
{
	_obj_ptr->~T ();
	_allo.deallocate (_obj_ptr, 1);
	_obj_ptr = nullptr;
}



template <class T, class A>
T *	SingleObj <T, A>::operator -> () const noexcept
{
	assert (_obj_ptr != nullptr);

	return _obj_ptr;
}



template <class T, class A>
T &	SingleObj <T, A>::operator * () const noexcept
{
	assert (_obj_ptr != 0);

	return *_obj_ptr;
}



/*\\\ PROTECTED \\\\\\\\\\\\\\\\\\\\\\\\\\\\\\\\\\\\\\\\\\\\\\\\\\\\\\\\\\\\*/



/*\\\ PRIVATE \\\\\\\\\\\\\\\\\\\\\\\\\\\\\\\\\\\\\\\\\\\\\\\\\\\\\\\\\\\\\\*/



}	// namespace fstb



#endif	// fstb_SingleObj_CODEHEADER_INCLUDED



/*\\\ EOF \\\\\\\\\\\\\\\\\\\\\\\\\\\\\\\\\\\\\\\\\\\\\\\\\\\\\\\\\\\\\\\\\\*/
