EleonoreMizo/pedalevite/src/fstb/CpuId.h

/*****************************************************************************

        CpuId.h
        Author: Laurent de Soras, 2012

--- Legal stuff ---

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
*Tab=3***********************************************************************/



#if ! defined (fstb_CpuId_HEADER_INCLUDED)
#define	fstb_CpuId_HEADER_INCLUDED

#if defined (_MSC_VER)
	#pragma once
	#pragma warning (4 : 4250)
#endif



/*\\\ INCLUDE FILES \\\\\\\\\\\\\\\\\\\\\\\\\\\\\\\\\\\\\\\\\\\\\\\\\\\\\\\\*/

#include "fstb/def.h"



namespace fstb
{



class CpuId
{

/*\\\ PUBLIC \\\\\\\\\\\\\\\\\\\\\\\\\\\\\\\\\\\\\\\\\\\\\\\\\\\\\\\\\\\\\\\*/

public:

	               CpuId ();
	               CpuId (const CpuId &other)      = default;

	CpuId &        operator = (const CpuId &other) = default;

#if fstb_ARCHI == fstb_ARCHI_X86
	static void		call_cpuid (unsigned int fnc_nbr, unsigned int subfnc_nbr, unsigned int &v_eax, unsigned int &v_ebx, unsigned int &v_ecx, unsigned int &v_edx);
#endif

	bool           _mmx_flag     = false;
	bool           _fxsr_flag    = false;  // FXSAVE, FXRESTOR, CR4 bit 9
	bool           _3dnow_flag   = false;
	bool           _isse_flag    = false;
	bool           _sse_flag     = false;
	bool           _sse2_flag    = false;
	bool           _sse3_flag    = false;
	bool           _ssse3_flag   = false;
	bool           _sse41_flag   = false;
	bool           _sse42_flag   = false;
	bool           _sse4a_flag   = false;
	bool           _fma3_flag    = false;
	bool           _fma4_flag    = false;
	bool           _avx_flag     = false;
	bool           _avx2_flag    = false;
	bool           _avx512f_flag = false;
	bool           _f16c_flag    = false;  // Half-precision FP
	bool           _cx16_flag    = false;  // CMPXCHG16B
	bool           _abm_flag     = false;  // POPCNT + LZCNT
	bool           _bmi1_flag    = false;  // Bit Manipulation Instruction Set
	bool           _bmi2_flag    = false;



/*\\\ PROTECTED \\\\\\\\\\\\\\\\\\\\\\\\\\\\\\\\\\\\\\\\\\\\\\\\\\\\\\\\\\\\*/

protected:



/*\\\ PRIVATE \\\\\\\\\\\\\\\\\\\\\\\\\\\\\\\\\\\\\\\\\\\\\\\\\\\\\\\\\\\\\\*/

private:



/*\\\ FORBIDDEN MEMBER FUNCTIONS \\\\\\\\\\\\\\\\\\\\\\\\\\\\\\\\\\\\\\\\\\\*/

private:

	bool           operator == (const CpuId &other) const = delete;
	bool           operator != (const CpuId &other) const = delete;

};	// class CpuId



}	// namespace fstb



//#include "fstb/CpuId.hpp"



#endif	// fstb_CpuId_HEADER_INCLUDED



/*\\\ EOF \\\\\\\\\\\\\\\\\\\\\\\\\\\\\\\\\\\\\\\\\\\\\\\\\\\\\\\\\\\\\\\\\\*/
