EleonoreMizo/pedalevite/src/fstb/BitFieldTools.hpp

/*****************************************************************************

        BitFieldTools.hpp
        Author: Laurent de Soras, 2006

--- Legal stuff ---

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
*Tab=3***********************************************************************/



#if ! defined (fstb_BitFieldTools_CODEHEADER_INCLUDED)
#define fstb_BitFieldTools_CODEHEADER_INCLUDED



/*\\\ INCLUDE FILES \\\\\\\\\\\\\\\\\\\\\\\\\\\\\\\\\\\\\\\\\\\\\\\\\\\\\\\\*/

#include "fstb/Err.h"

#include <cassert>



namespace fstb
{



/*\\\ PUBLIC \\\\\\\\\\\\\\\\\\\\\\\\\\\\\\\\\\\\\\\\\\\\\\\\\\\\\\\\\\\\\\\*/



template <typename T, int DL2>
int	BitFieldTools <T, DL2>::calculate_nbr_groups (int nbr_elt) noexcept
{
	assert (nbr_elt > 0);

	const int      nbr_groups = ((nbr_elt - 1) >> BITDEPTH_L2) + 1;
	assert (nbr_groups > 0);

	return (nbr_groups);
}



template <typename T, int DL2>
void	BitFieldTools <T, DL2>::calculate_group_and_pos (int &group, int &gpos, int pos) noexcept
{
	assert (pos >= 0);

	group = (pos >> BITDEPTH_L2);
	gpos  = int (pos & (BITDEPTH - 1));
}



template <typename T, int DL2>
void	BitFieldTools <T, DL2>::calculate_group_and_mask (int &group, GroupType &mask, int pos) noexcept
{
	assert (pos >= 0);

	int            gpos;
	calculate_group_and_pos (group, gpos, pos);
	mask = GroupType (1) << gpos;
}



template <typename T, int DL2>
bool	BitFieldTools <T, DL2>::get_bit (const GroupType bit_arr [], int pos) noexcept
{
	assert (pos >= 0);

	int            group;
	GroupType      mask;
	calculate_group_and_mask (group, mask, pos);

	return ((bit_arr [group] & mask) != 0);
}



template <typename T, int DL2>
void	BitFieldTools <T, DL2>::set_bit (GroupType bit_arr [], int pos, bool flag) noexcept
{
	assert (bit_arr != nullptr);
	assert (pos >= 0);

	int            group;
	GroupType      mask;
	calculate_group_and_mask (group, mask, pos);

	if (flag)
	{
		bit_arr [group] |= mask;
	}
	else
	{
		bit_arr [group] &= ~mask;
	}
}
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
